digamesystems/LIDAR/docs/Heimdall Docs/FCC Label/FCC_Label.pdf

M

# Dígame Systems odel: DS-VC-LIDAR-LOR-1

FCC IDS: QLYRYLR896, 2AC7Z-ESPWROOM32

www.digamesystems.com Made in USA

### HEMDALL VCS Vehicle Counting System

M

# Dígame Systems odel: DS-VC-LIDAR-LOR-1

FCC IDS: QLYRYLR896, 2AC7Z-ESPWROOM32

www.digamesystems.com Made in USA

### HEMDALL VCS Vehicle Counting System

M

# Dígame Systems odel: DS-VC-LIDAR-LOR-1

FCC IDS: QLYRYLR896, 2AC7Z-ESPWROOM32

www.digamesystems.com Made in USA

### HEMDALL VCS Vehicle Counting System

M

# Dígame Systems odel: DS-VC-LIDAR-LOR-1

FCC IDS: QLYRYLR896, 2AC7Z-ESPWROOM32

www.digamesystems.com Made in USA

### HEMDALL VCS Vehicle Counting System

M

# Dígame Systems odel: DS-VC-LIDAR-LOR-1

FCC IDS: QLYRYLR896, 2AC7Z-ESPWROOM32

www.digamesystems.com Made in USA

### HEMDALL VCS Vehicle Counting System

M

# Dígame Systems odel: DS-VC-LIDAR-LOR-1

FCC IDS: QLYRYLR896, 2AC7Z-ESPWROOM32

www.digamesystems.com Made in USA

### HEMDALL VCS Vehicle Counting System

M

# Dígame Systems odel: DS-VC-LIDAR-LOR-1

FCC IDS: QLYRYLR896, 2AC7Z-ESPWROOM32

www.digamesystems.com Made in USA

### HEMDALL VCS Vehicle Counting System

M

# Dígame Systems odel: DS-VC-LIDAR-LOR-1

FCC IDS: QLYRYLR896, 2AC7Z-ESPWROOM32

www.digamesystems.com Made in USA

### HEMDALL VCS Vehicle Counting System

M

# Dígame Systems odel: DS-VC-LIDAR-LOR-1

FCC IDS: QLYRYLR896, 2AC7Z-ESPWROOM32

www.digamesystems.com Made in USA

### HEMDALL VCS Vehicle Counting System

M

# Dígame Systems odel: DS-VC-LIDAR-LOR-1

FCC IDS: QLYRYLR896, 2AC7Z-ESPWROOM32

www.digamesystems.com Made in USA

### HEMDALL VCS Vehicle Counting System

M

# Dígame Systems odel: DS-VC-LIDAR-LOR-1

FCC IDS: QLYRYLR896, 2AC7Z-ESPWROOM32

www.digamesystems.com Made in USA

### HEMDALL VCS Vehicle Counting System

M

# Dígame Systems odel: DS-VC-LIDAR-LOR-1

FCC IDS: QLYRYLR896, 2AC7Z-ESPWROOM32

www.digamesystems.com Made in USA

### HEMDALL VCS Vehicle Counting System

M

# Dígame Systems odel: DS-VC-LIDAR-LOR-1

FCC IDS: QLYRYLR896, 2AC7Z-ESPWROOM32

www.digamesystems.com Made in USA

### HEMDALL VCS Vehicle Counting System

M

# Dígame Systems odel: DS-VC-LIDAR-LOR-1

FCC IDS: QLYRYLR896, 2AC7Z-ESPWROOM32

www.digamesystems.com Made in USA

### HEMDALL VCS Vehicle Counting System

M

# Dígame Systems odel: DS-VC-LIDAR-LOR-1

FCC IDS: QLYRYLR896, 2AC7Z-ESPWROOM32

www.digamesystems.com Made in USA

### HEMDALL VCS Vehicle Counting System
