digamesystems/LIDAR/docs/Heimdall Docs/Product Brief/Heimdall VCS Digame Systems v 1.1.pdf

# Heimdall VCS

# ANONYMOUS, ACCURATE VEHICLE COUNTING— WITHOUT TOUCHING THE ROADWAY

# The Heimdall VCS is a cutting-edge vehicle counting system incorporating recent technology advancements in high-performance sensors, wireless connectivity, and artificial intelligence

to provide unprecedented performance at an affordable price.

# FEATURES AND FUNCTIONS

### - LIDAR-Based solution means vehicles can be counted without hardware on the roadway –

Allowing lower installation and maintenance costs.

### - Respects privacy – The system does not make use

of cameras.

- Outdoor Rated – IP67, NEMA4.

### - WiFi with optional LoRaWAN (Low power, Long Range RF link) or cellular connectivity. – Requires

no external wiring to the unit.

- Easy integration with back-end systems – Secure, HTTPs API.
- Battery-backed solar power for reliable, autonomous operation.

### - Accurate target determination at up to 12 meters

of range.

### - Advanced signal processing allows reliable

operation in rain and fog.

## HEIMDALL VCS SPECIFICATIONS

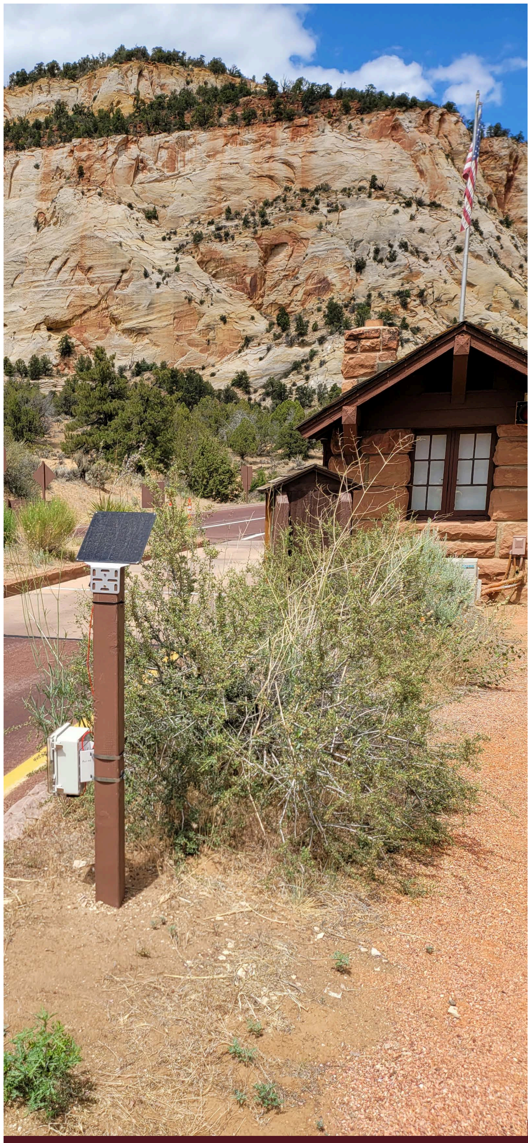
[picture p3: figure]

Use Case

LIDAR Sensor Specifications

Mounting / Power

Interface / Communications

Environmental

Vehicle counting
applications:

Vehicle speed:

Operating Range

Accuracy:

Field of View:

Frame Rate:

Counting Accuracy:

Mounting:

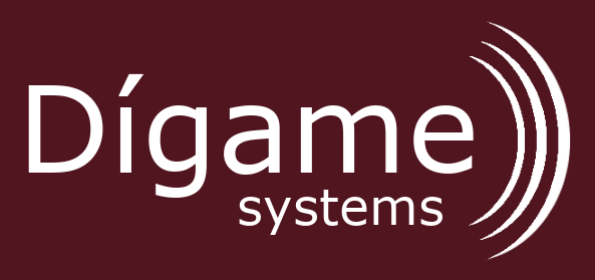
[picture p4: figure]

Input Voltage:

Power Consumption:

Battery:

Battery Type:

Protection:

Cellular service:

Security:

API:

Enclosure:

Operational Temperature:

Storage Temperature

Warranty:

WiFi, Cellular, LoRaWan:

1-2 Lanes of traffic.

Up to 60 MPH

0.1 – 12 meters

+/- 5 cm

3.6 degrees

100 Hz

>95% counting accuracy at distances < 12

### meters and speeds < 60 MPH. (Performance may vary in extreme weather conditions.)

Surface mount or pole mount (custom options available)

5-7 VDC (DC power supply or supplied solar panel output)

1 Watt typ.

Capacity: 12,800mAh, 47 Watt Hours

Li-Ion

Short circuit over charge, over discharge, over temperature (45°Input Cutoff, 60° Output Cutoff), under temperature (0° Input Cutoff, -20° Output Cutoff)

WiFi included. Cellular and LoRaWAN optional.

HTTPs, WPA under WiFI

JSON-based for easy integration

High Impact UV resistant polycarbonate, IP67/NEMA4

20° to + 60°

-20°C to +60°C

Replacement, 3 years parts and labor.

Dígame Systems

88 E San Fernando St. Suite 1511 San Jose, CA 95113

+1 408.840.9871
info@digamesystems.com

## Ready to get started?

Contact info@digamesystems.com

Not included.
