digamesystems/LIDAR/docs/shuttleCutFiles/TF-mini Plus Diagrams/982B110B7F3D70D8.png

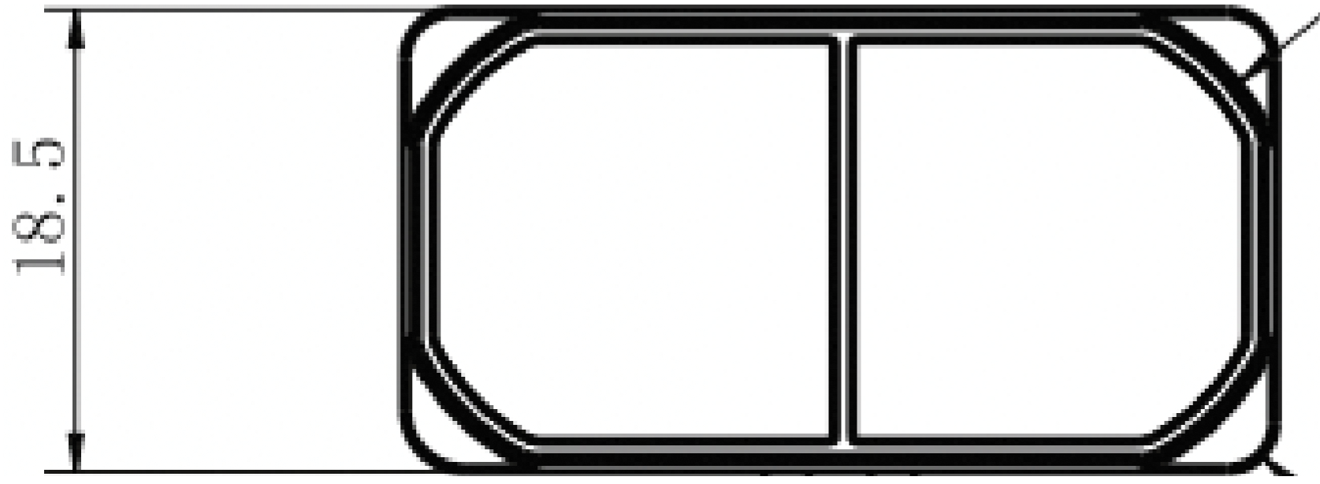
docs/shuttleCutFiles/TF-mini Plus Diagrams/982B110B7F3D70D8.png
