digamesystems/LIDAR/docs/shuttleCutFiles/TF-mini Plus Diagrams/982B110B7F3D70DF.jpg

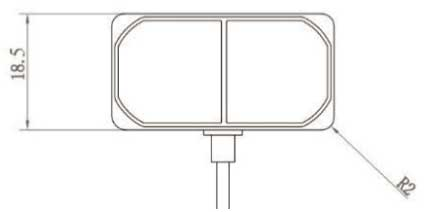
docs/shuttleCutFiles/TF-mini Plus Diagrams/982B110B7F3D70DF.jpg
