digamesystems/LIDAR/images/200x200_BMPS/digame.bmp

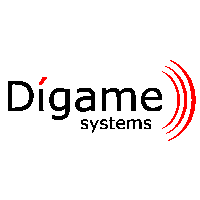
images/200x200_BMPS/digame.bmp
