digamesystems/LIDAR/images/200x200_BMPS/parkdata.bmp

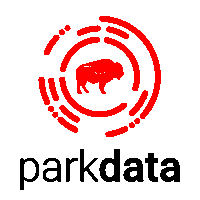
images/200x200_BMPS/parkdata.bmp
