digamesystems/LIDAR/images/200x200_BMPS/title.bmp

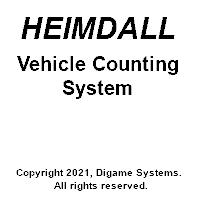
images/200x200_BMPS/title.bmp
