digamesystems/LIDAR/images/20210713_194357.jpg

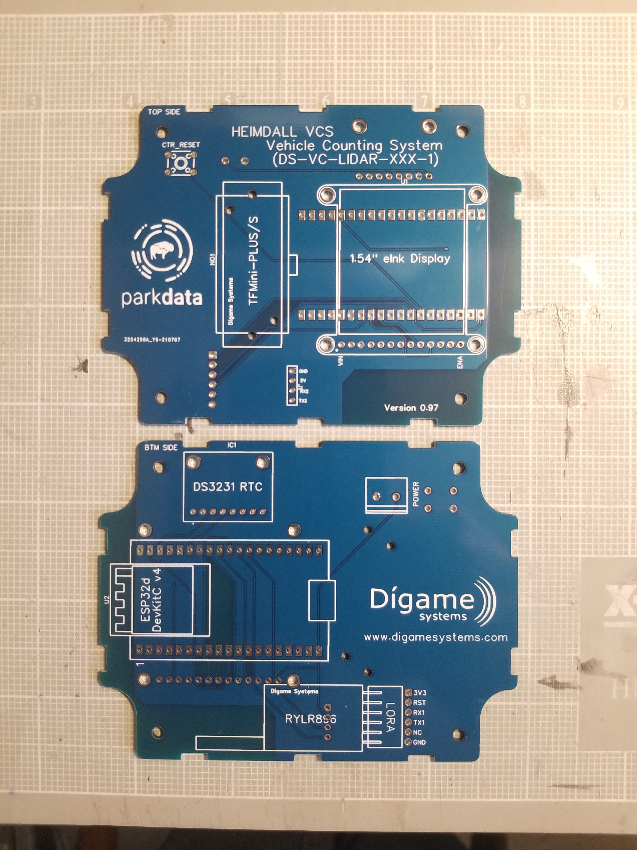
images/20210713_194357.jpg
