digamesystems/LIDAR/images/20210716_140122.jpg

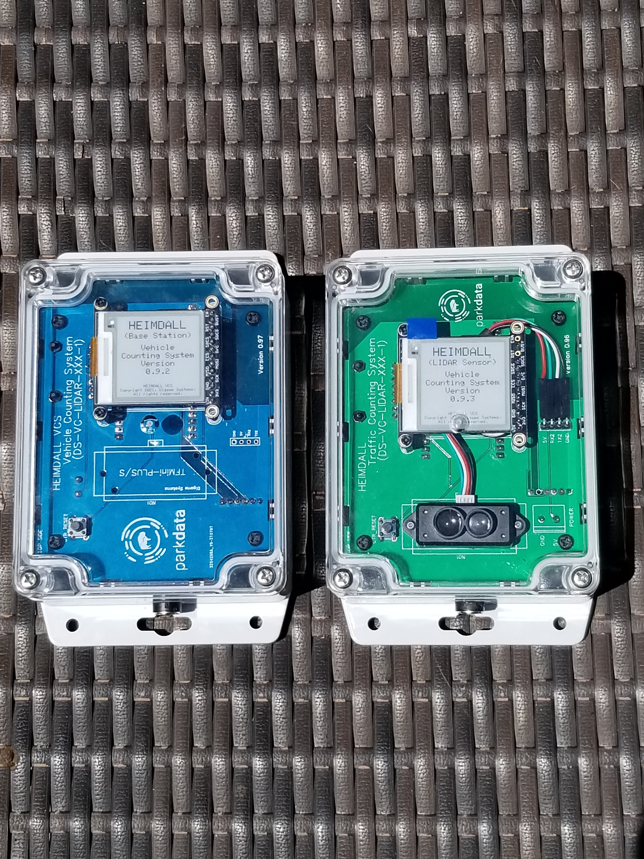
images/20210716_140122.jpg
