digamesystems/LIDAR/images/20210716_140350.jpg

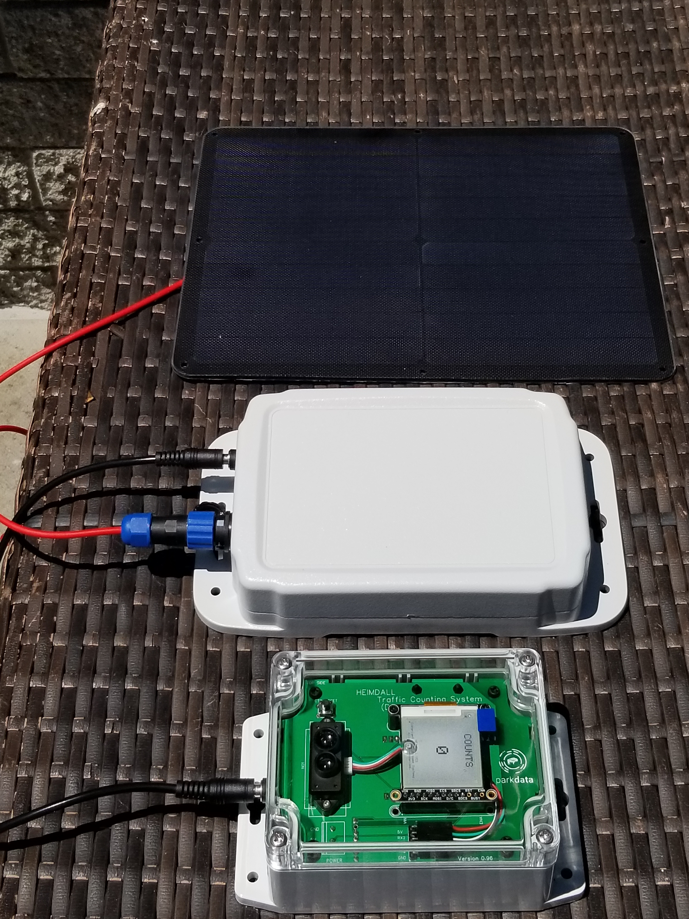
images/20210716_140350.jpg
