digamesystems/LIDAR/images/20210716_140622.jpg

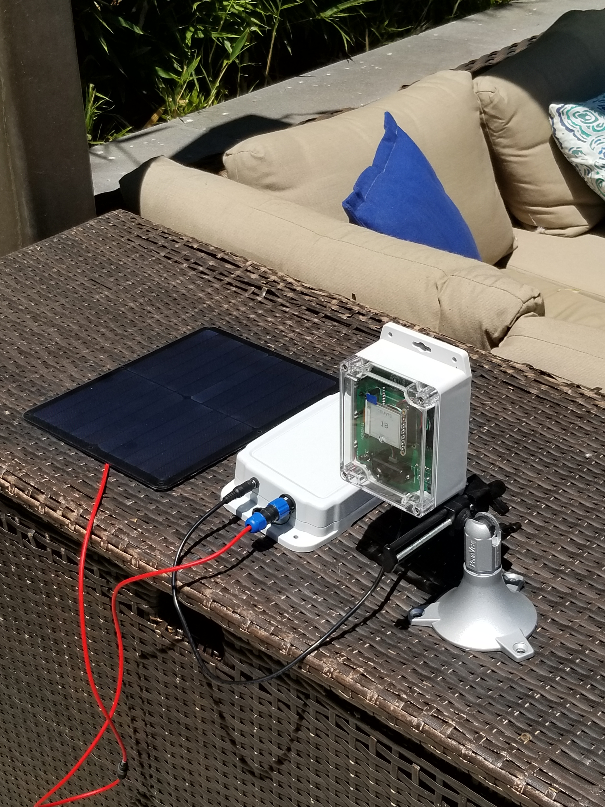
images/20210716_140622.jpg
