digamesystems/LIDAR/images/20210716_140631.jpg

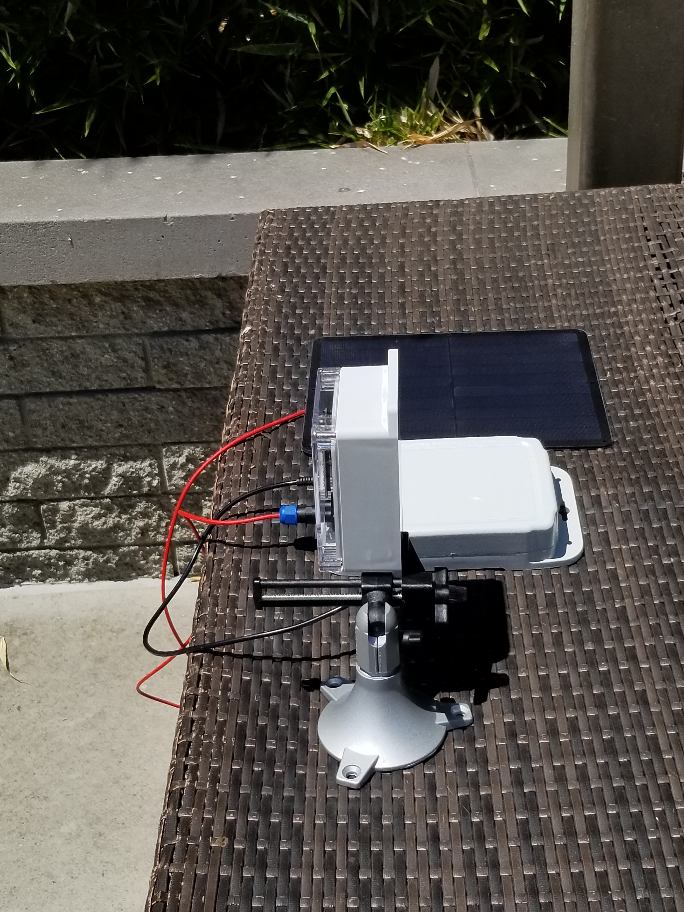
images/20210716_140631.jpg
