digamesystems/LIDAR/images/20210716_140637.jpg

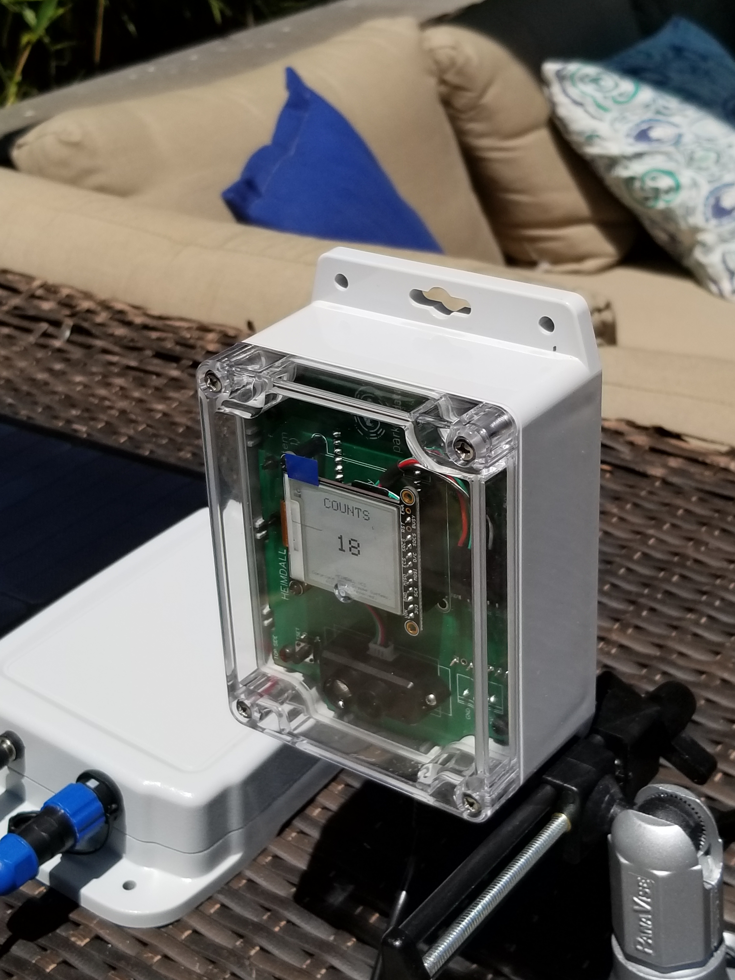
images/20210716_140637.jpg
