digamesystems/LIDAR/images/Heimdall Pics/2022-01-09 10.08.08.jpg

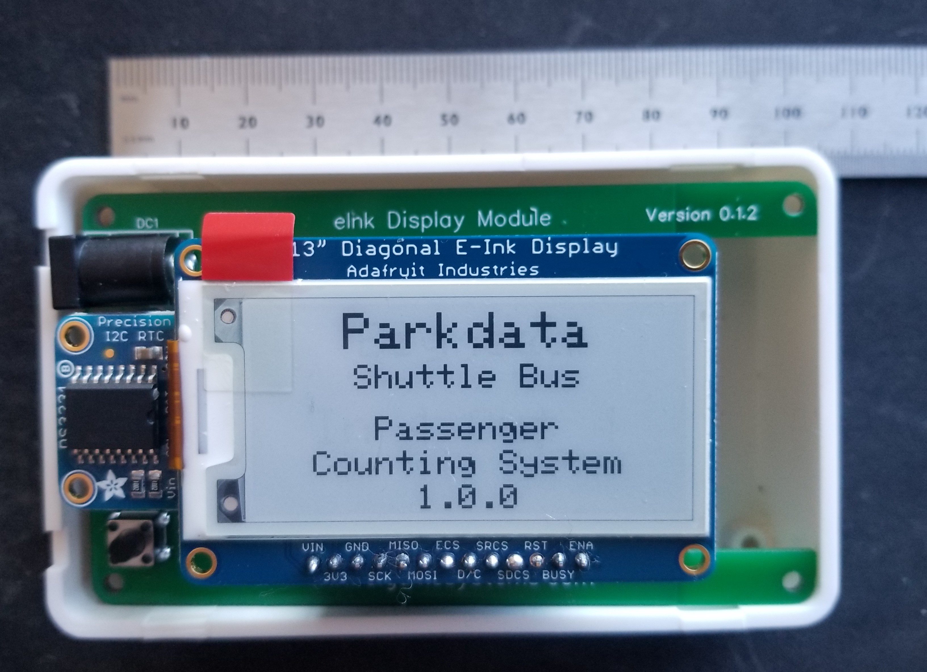
images/Heimdall Pics/2022-01-09 10.08.08.jpg
