digamesystems/LIDAR/images/Heimdall Pics/2022-01-11 13.43.02.jpg

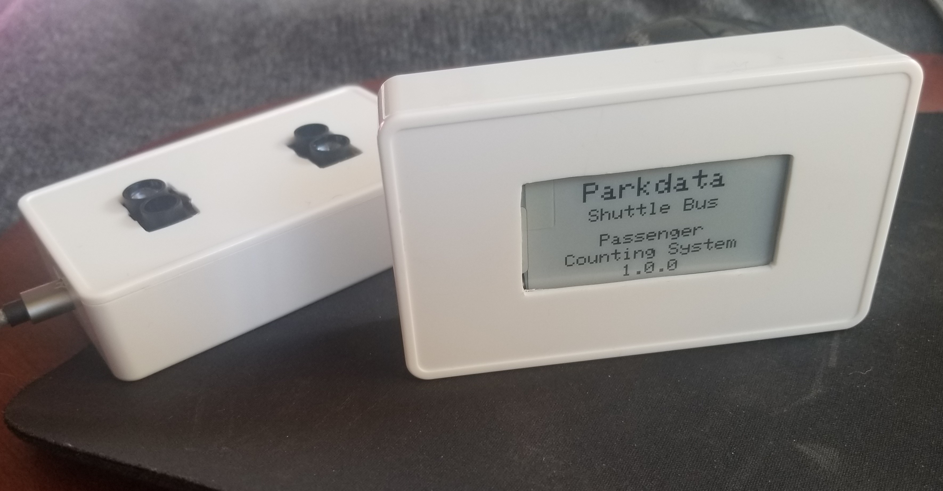
images/Heimdall Pics/2022-01-11 13.43.02.jpg
