digamesystems/LIDAR/images/Heimdall Pics/EastRadar_Dec21.PNG

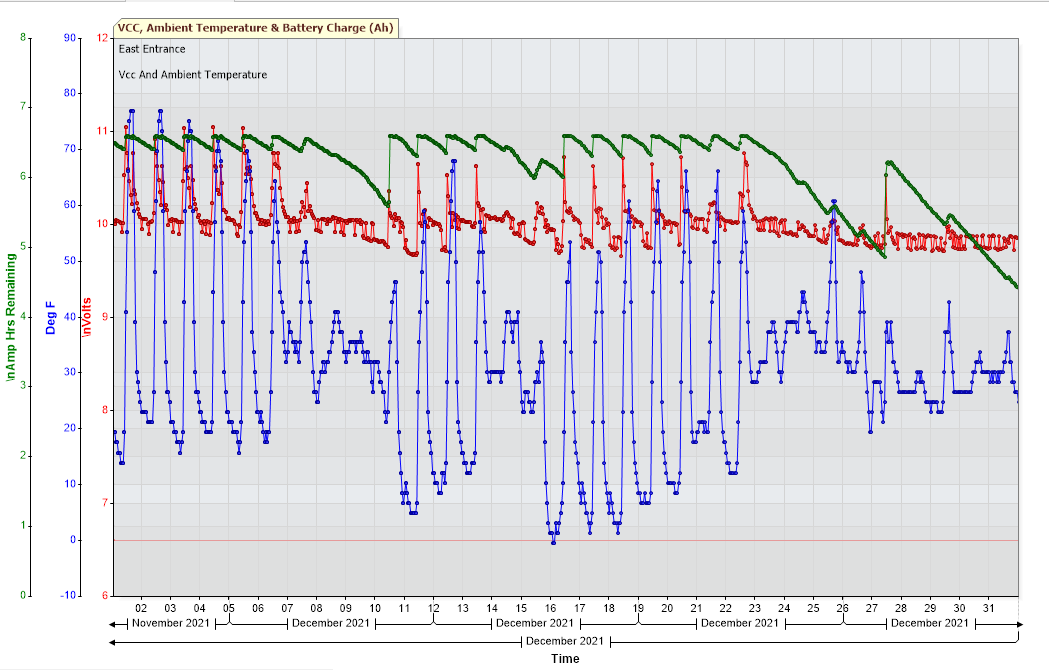
images/Heimdall Pics/EastRadar_Dec21.PNG
