digamesystems/LIDAR/images/Heimdall Pics/Zion Visitors Center 2.jpg

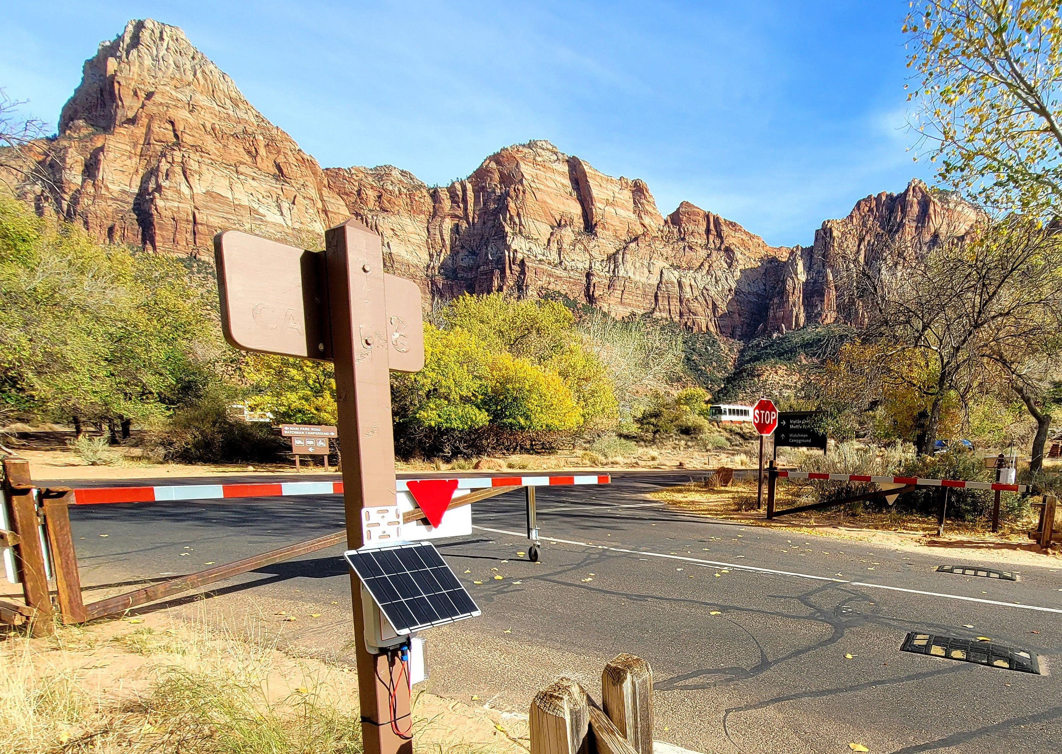
images/Heimdall Pics/Zion Visitors Center 2.jpg
