digamesystems/LIDAR/images/LoRa Examples/LoRa Tx and Rx Examples Working Together.png

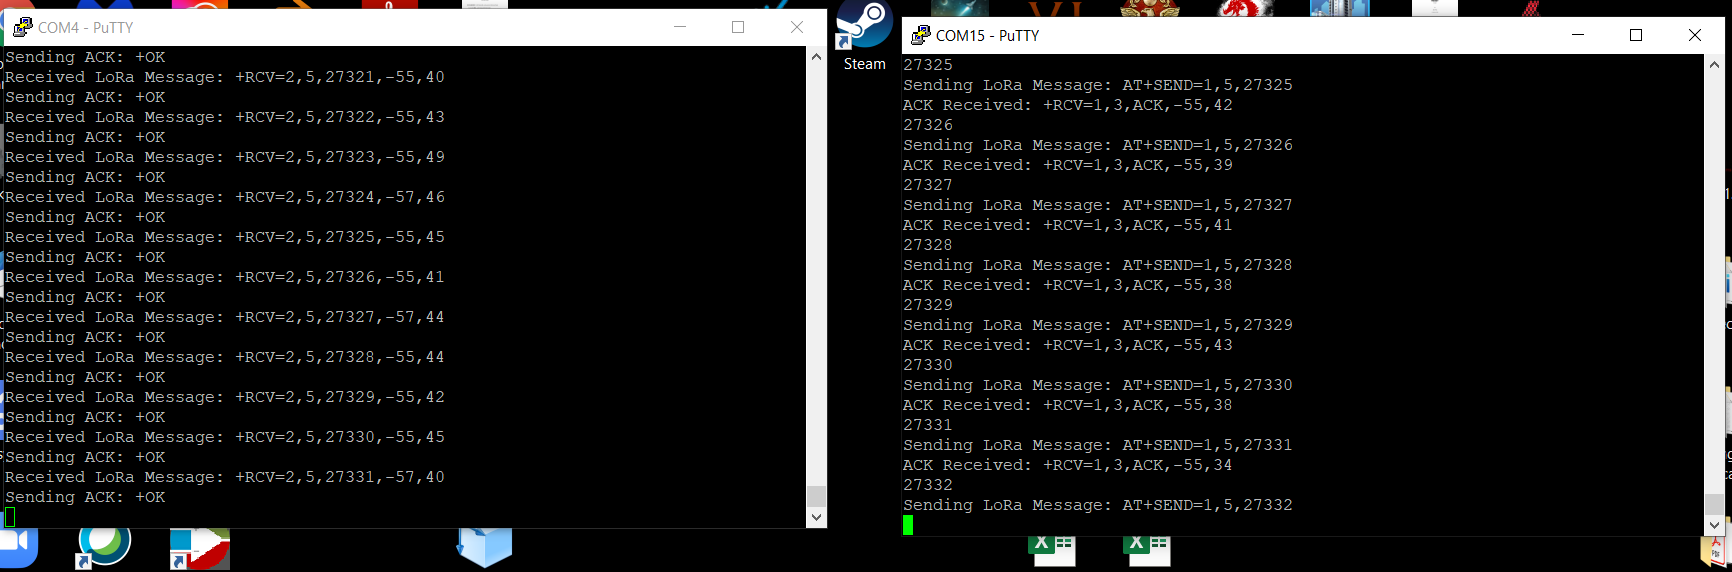
images/LoRa Examples/LoRa Tx and Rx Examples Working Together.png
