digamesystems/LIDAR/images/Shuttle Counter Pics/2021-12-30 08.01.03.jpg

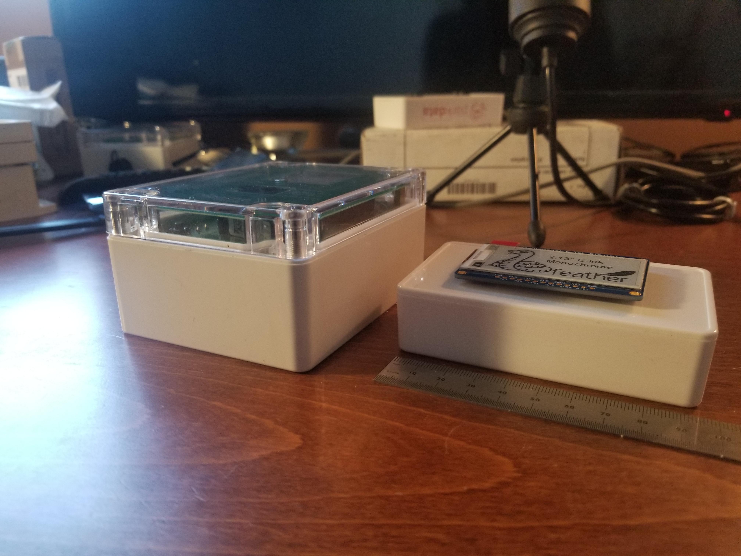
images/Shuttle Counter Pics/2021-12-30 08.01.03.jpg
