digamesystems/LIDAR/images/Shuttle Counter Pics/2022-01-10 12.27.30.jpg

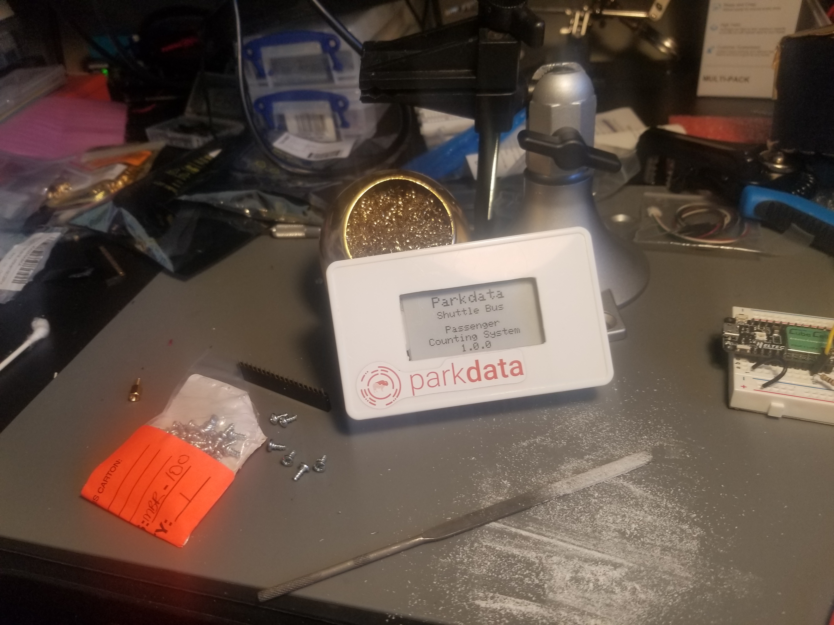
images/Shuttle Counter Pics/2022-01-10 12.27.30.jpg
