digamesystems/LIDAR/images/Shuttle Counter Pics/2022-01-20 13.23.47.jpg

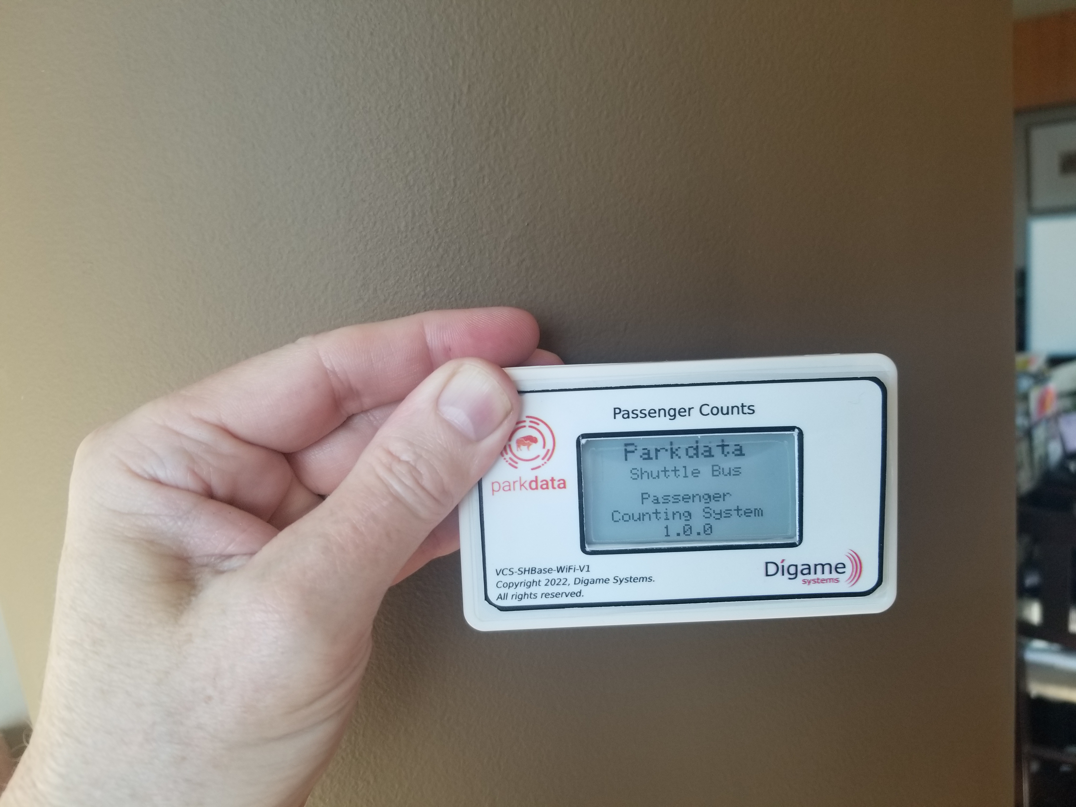
images/Shuttle Counter Pics/2022-01-20 13.23.47.jpg
