digamesystems/LIDAR/images/Shuttle Counter Pics/2022-03-01 12.52.25.jpg

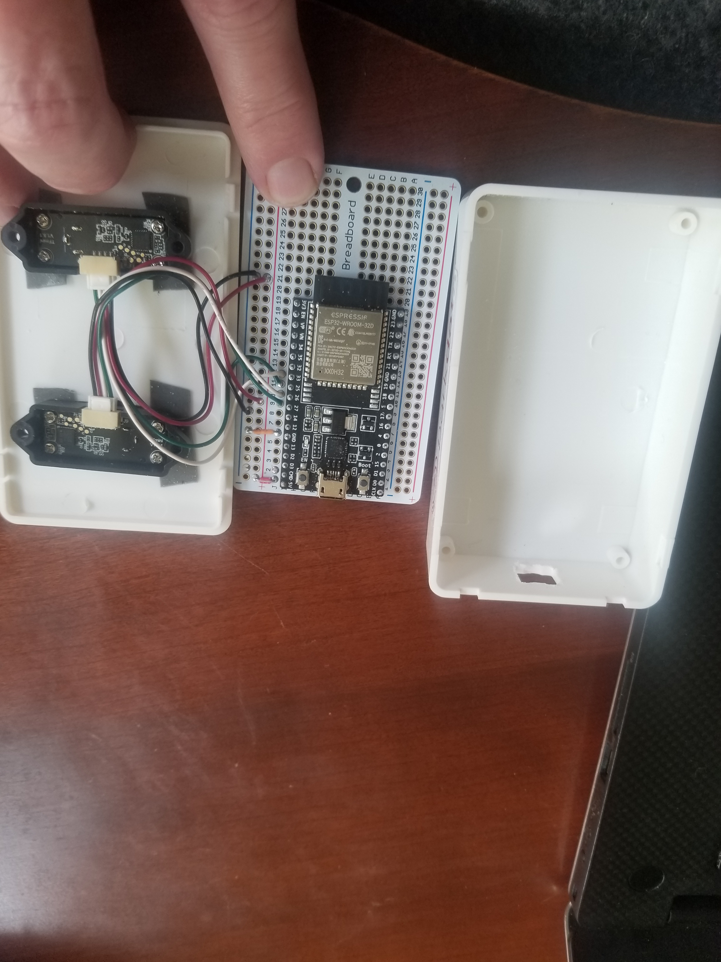
images/Shuttle Counter Pics/2022-03-01 12.52.25.jpg
