digamesystems/LIDAR/images/Shuttle Counter Pics/2022-03-01 12.52.33.jpg

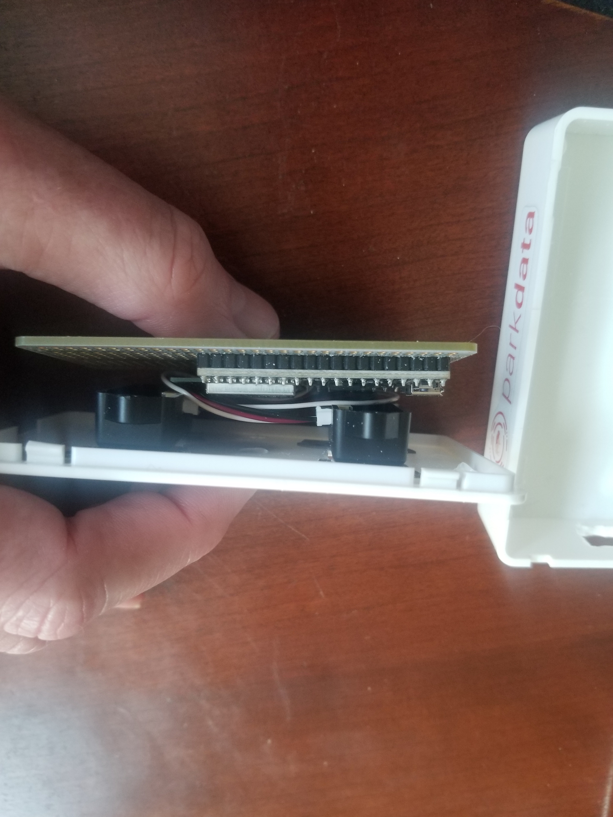
images/Shuttle Counter Pics/2022-03-01 12.52.33.jpg
