digamesystems/LIDAR/images/Shuttle Counter Pics/20220109_121842.jpg

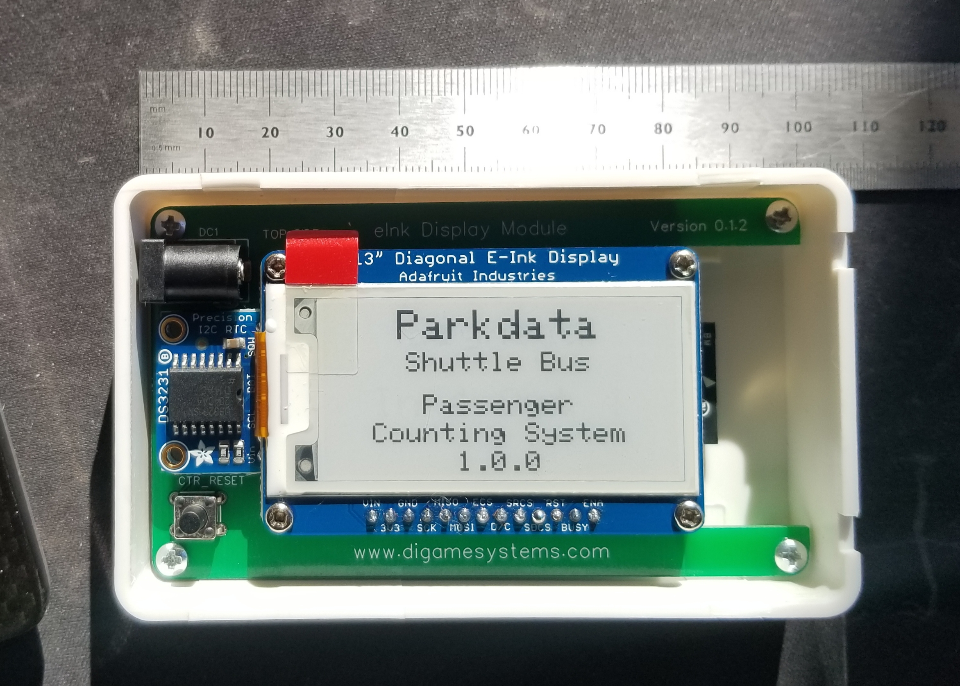
images/Shuttle Counter Pics/20220109_121842.jpg
