digamesystems/LIDAR/images/Shuttle Counter Pics/Image from iOS3.jpg

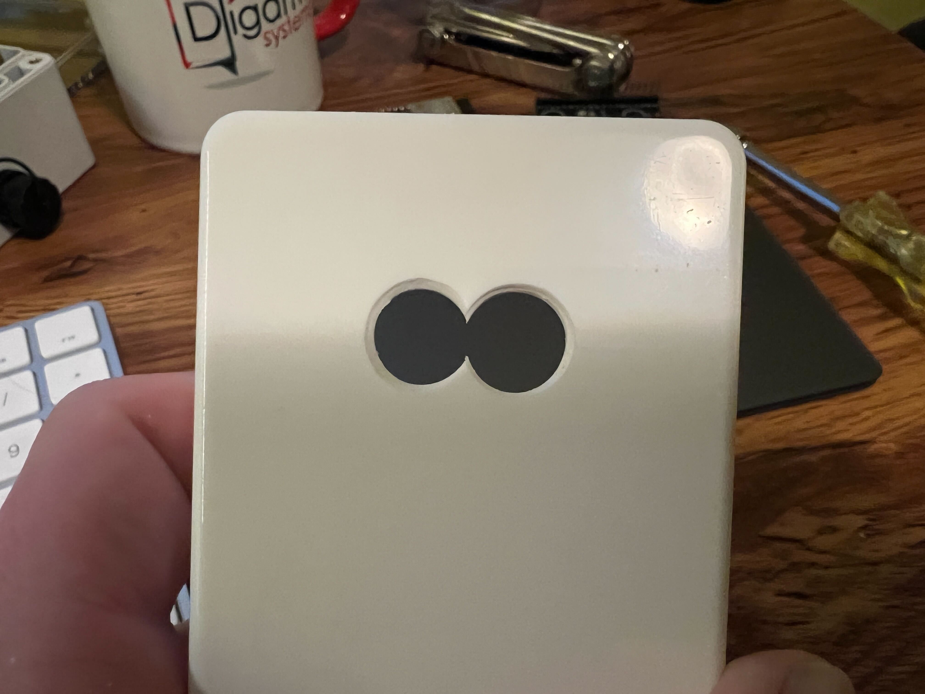
images/Shuttle Counter Pics/Image from iOS3.jpg
