digamesystems/LIDAR/images/Shuttle Counter Pics/Image from iOS 2.jpg

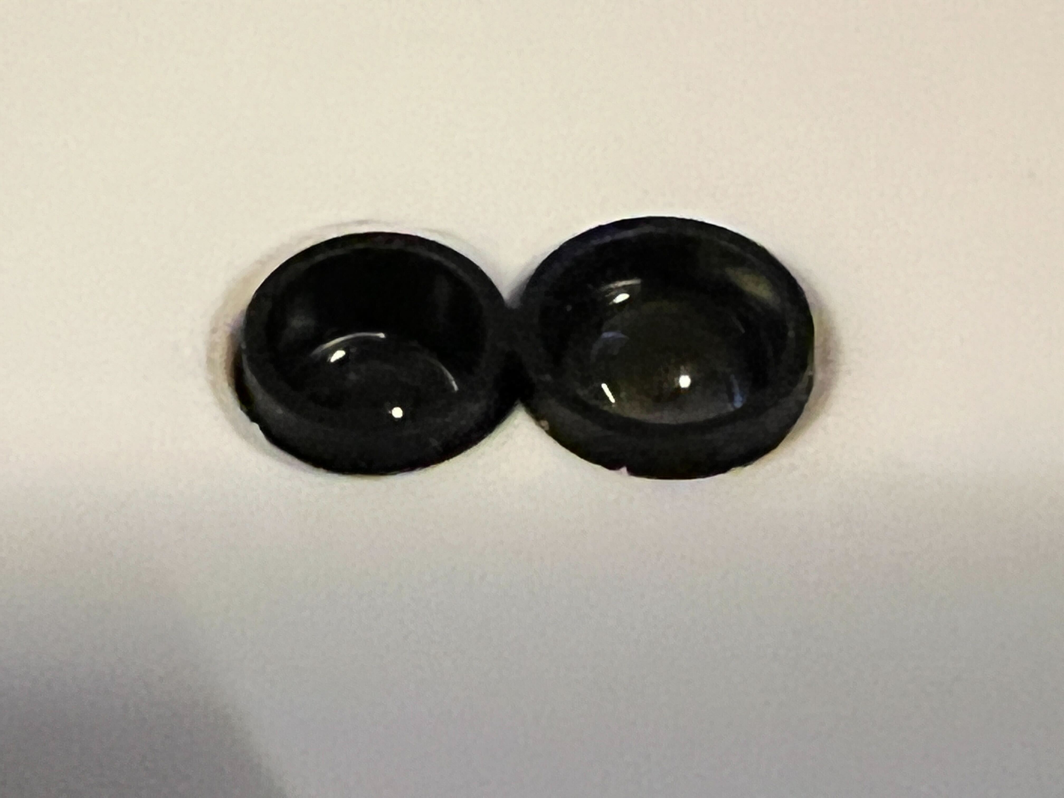
images/Shuttle Counter Pics/Image from iOS 2.jpg
