digamesystems/LIDAR/images/Shuttle Counter Pics/Image from iOS.jpg

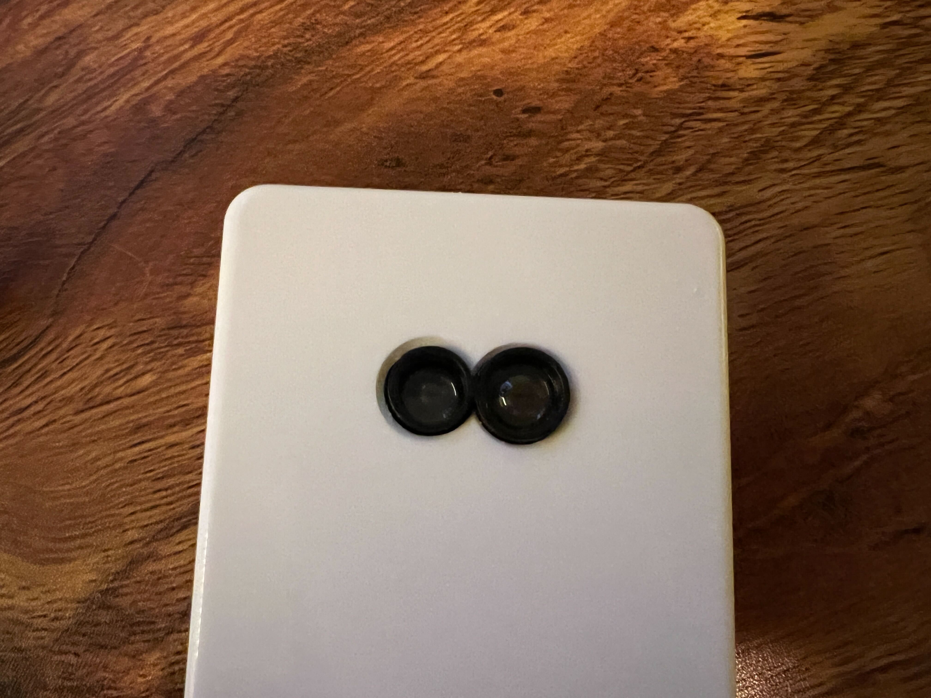
images/Shuttle Counter Pics/Image from iOS.jpg
