digamesystems/LIDAR/images/Shuttle Counter/20211229_122132.jpg

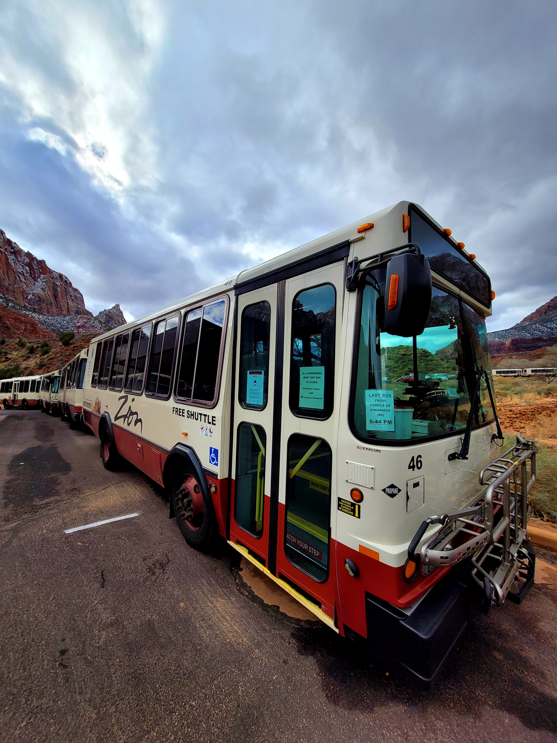
images/Shuttle Counter/20211229_122132.jpg
