digamesystems/LIDAR/images/Shuttle Counter/countingFingers.png

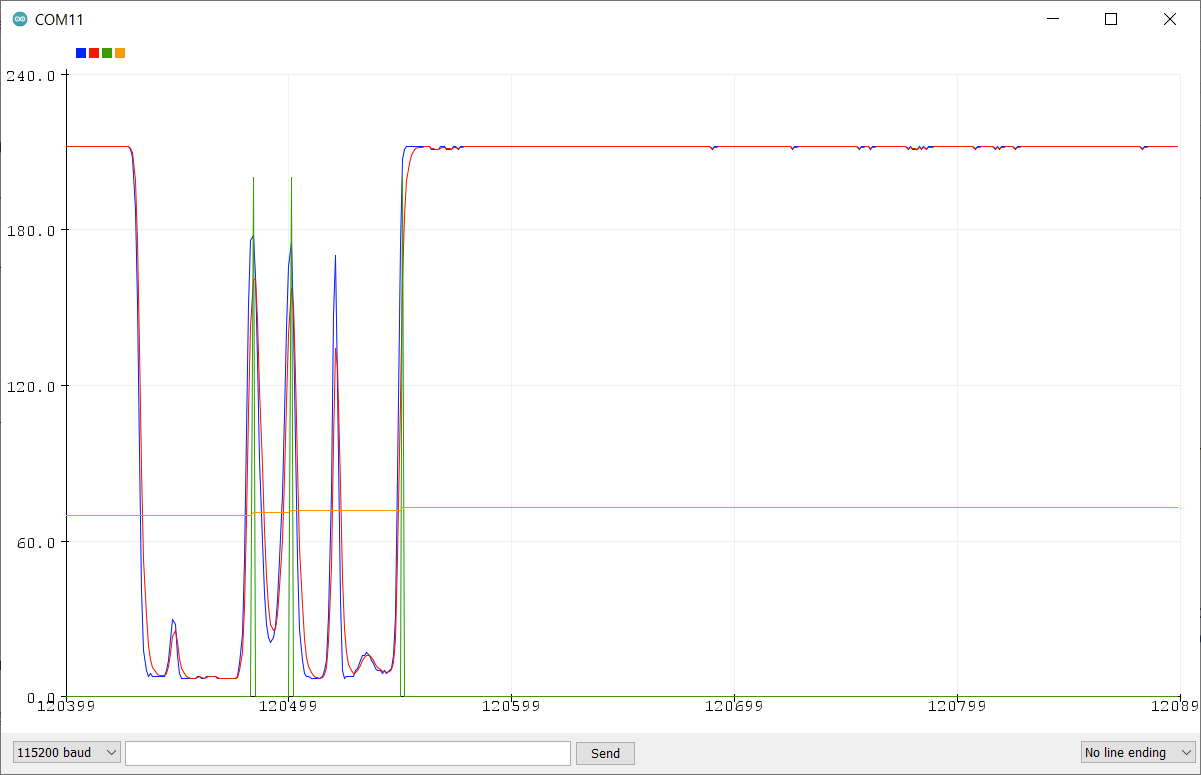
images/Shuttle Counter/countingFingers.png
