digamesystems/LIDAR/images/Shuttle Counter/filteredLIDARSignal.png

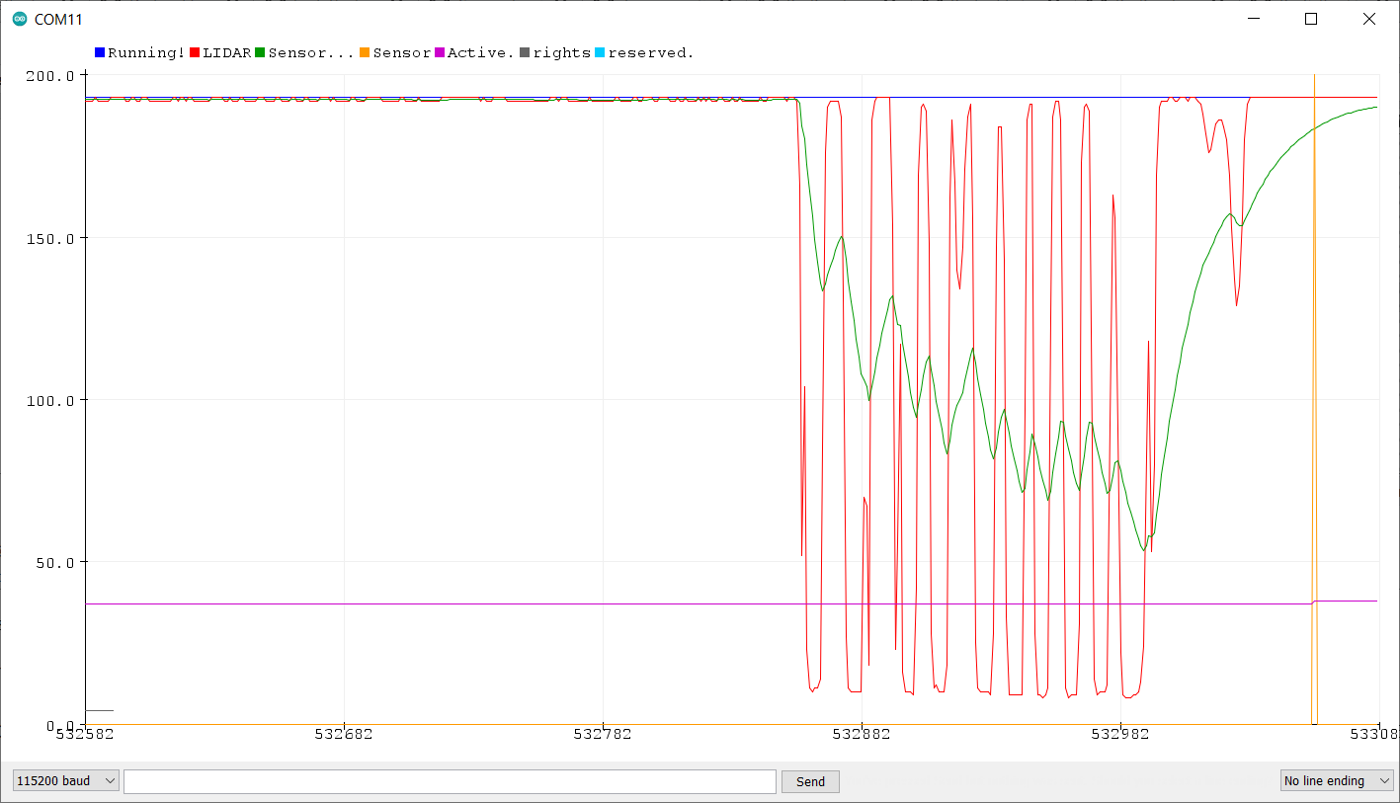
images/Shuttle Counter/filteredLIDARSignal.png
