digamesystems/LIDAR/images/Shuttle Counter/tfminiplusBeamWidth.png

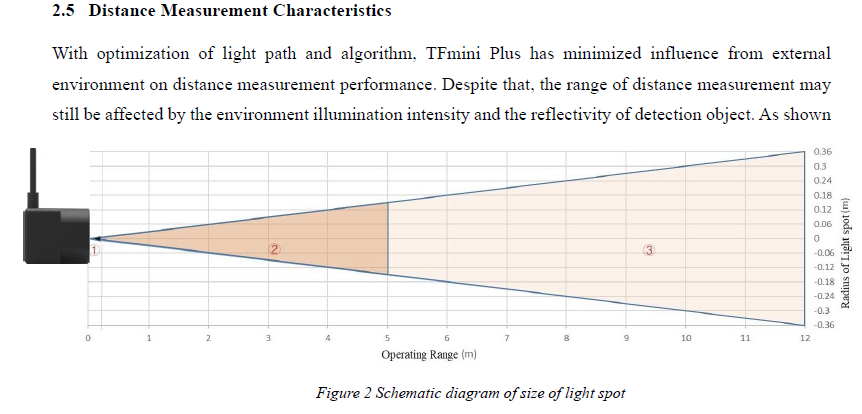
images/Shuttle Counter/tfminiplusBeamWidth.png
