digamesystems/LIDAR/images/Vehicle Counter/20201228_115122.jpg

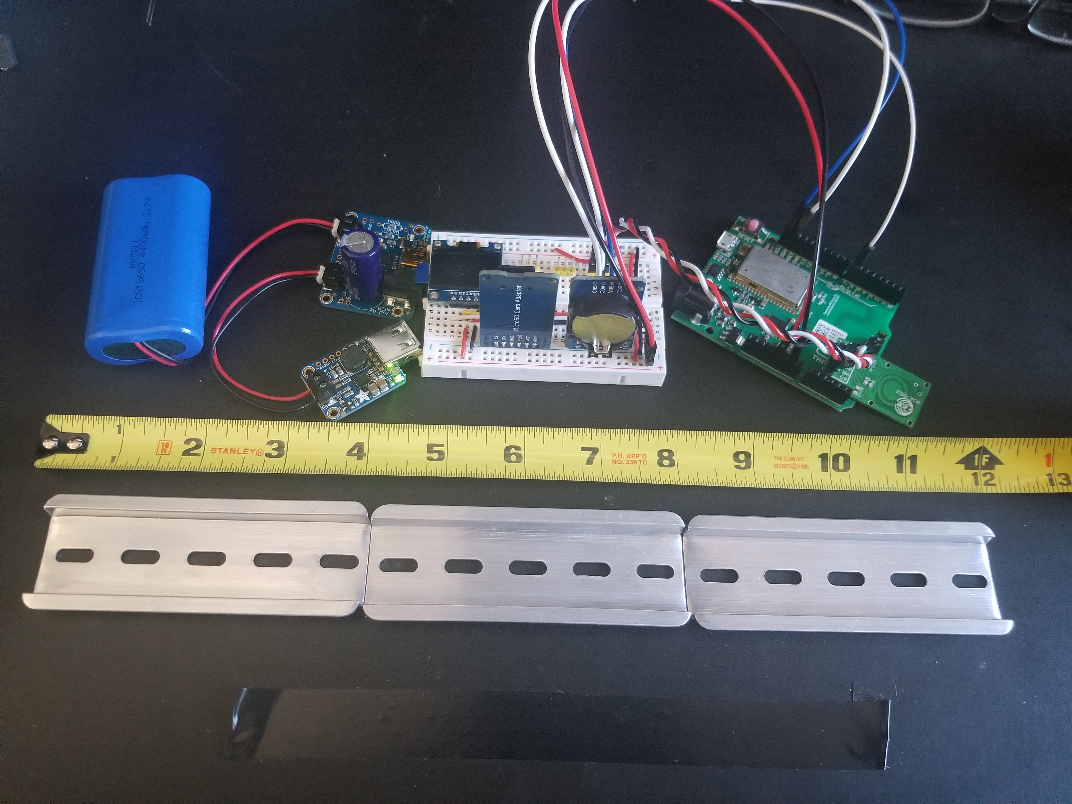
images/Vehicle Counter/20201228_115122.jpg
