digamesystems/LIDAR/images/Vehicle Counter/20201228_115124.jpg

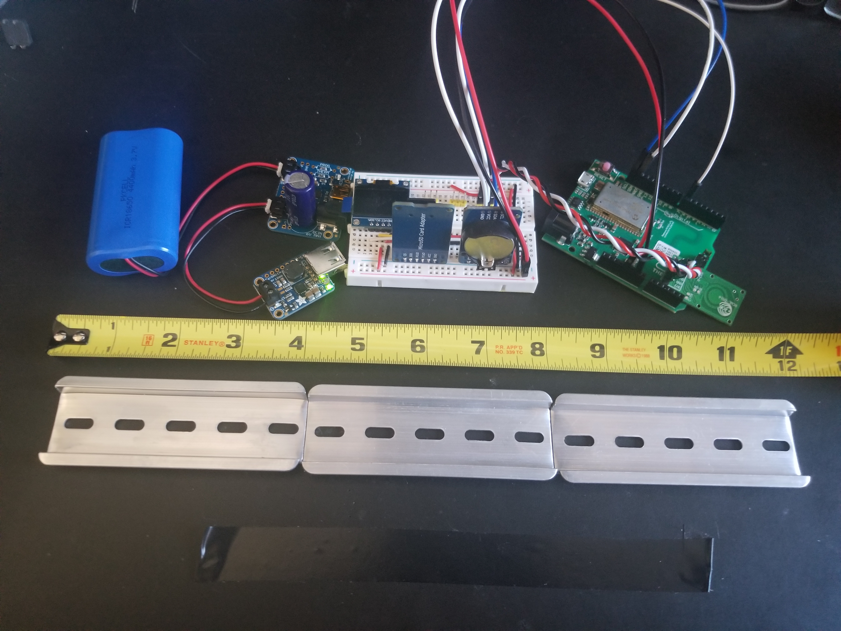
images/Vehicle Counter/20201228_115124.jpg
