digamesystems/LIDAR/images/Vehicle Counter/20210312_141206.jpg

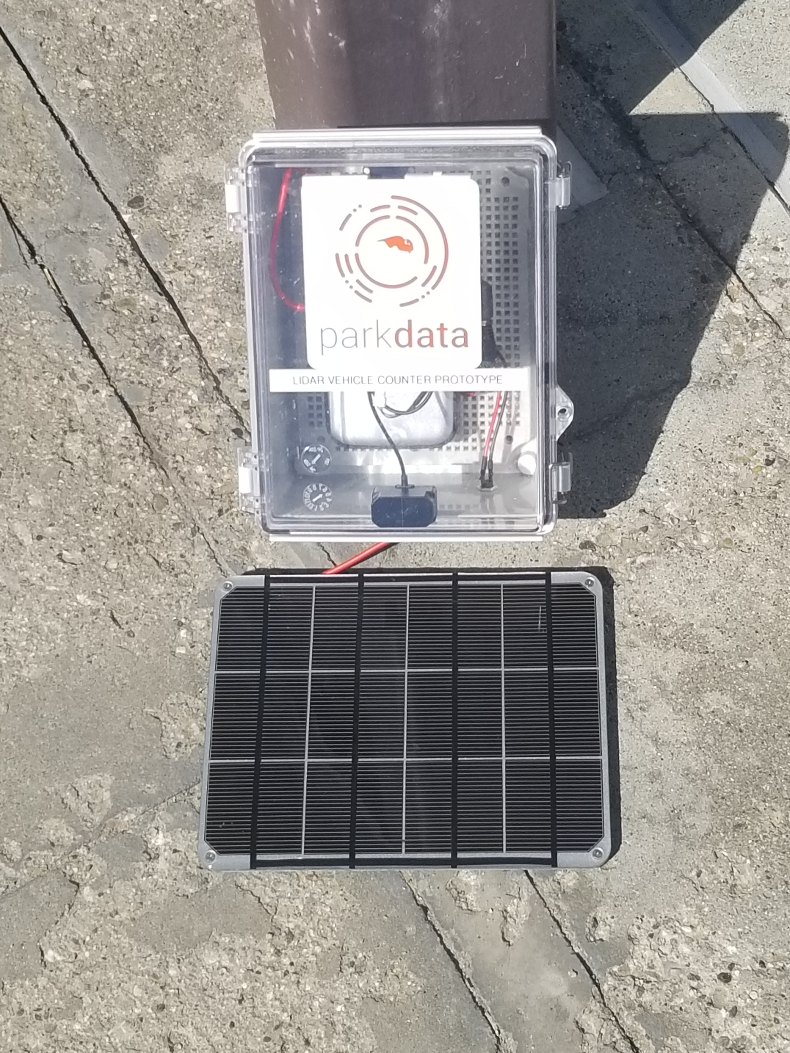
images/Vehicle Counter/20210312_141206.jpg
