digamesystems/LIDAR/images/Vehicle Counter/20210315_130030 zoom.jpg

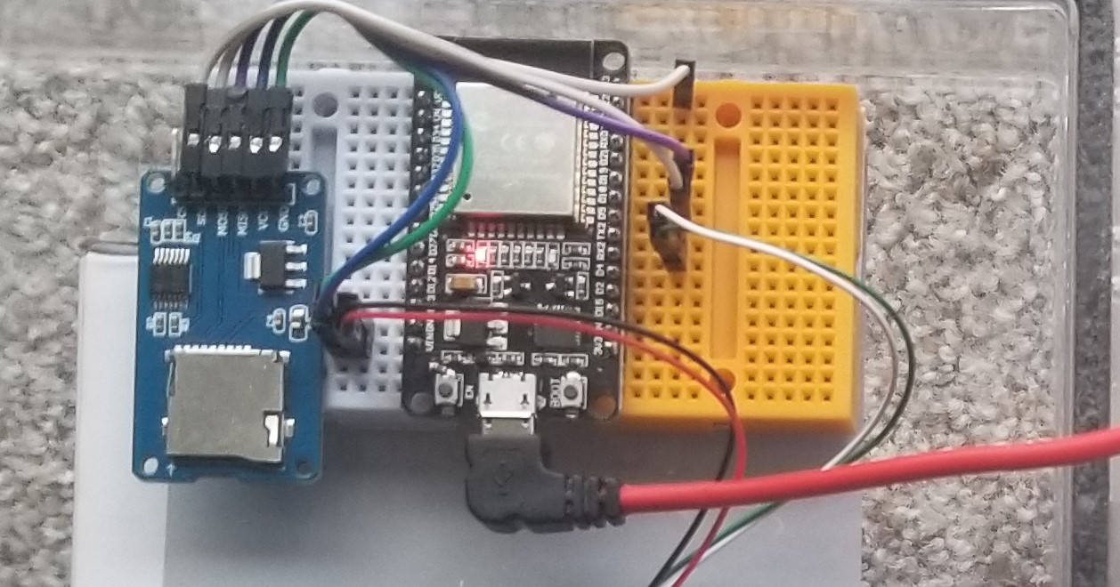
images/Vehicle Counter/20210315_130030 zoom.jpg
