digamesystems/LIDAR/images/Vehicle Counter/20210509_163343.jpg

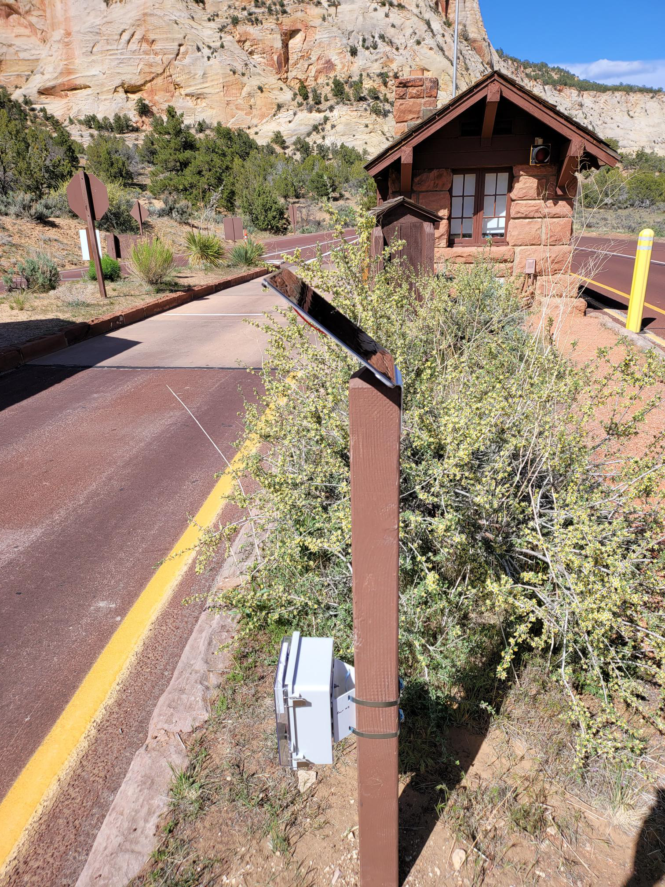
images/Vehicle Counter/20210509_163343.jpg
