digamesystems/LIDAR/images/Vehicle Counter/20210514_175608.jpg

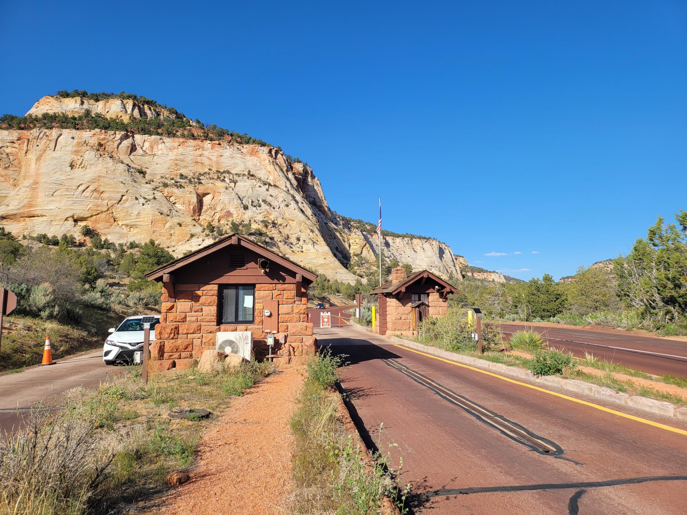
images/Vehicle Counter/20210514_175608.jpg
