digamesystems/LIDAR/images/Vehicle Counter/20210520_163920.jpg

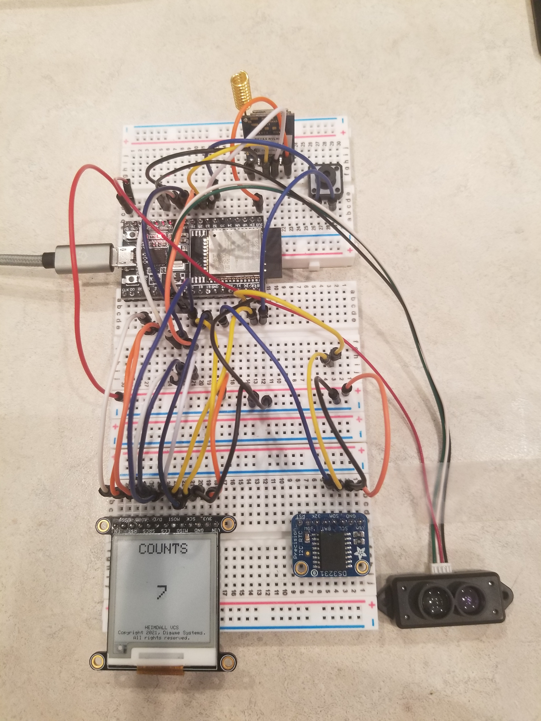
images/Vehicle Counter/20210520_163920.jpg
