digamesystems/LIDAR/images/Vehicle Counter/20211015_151012.jpg

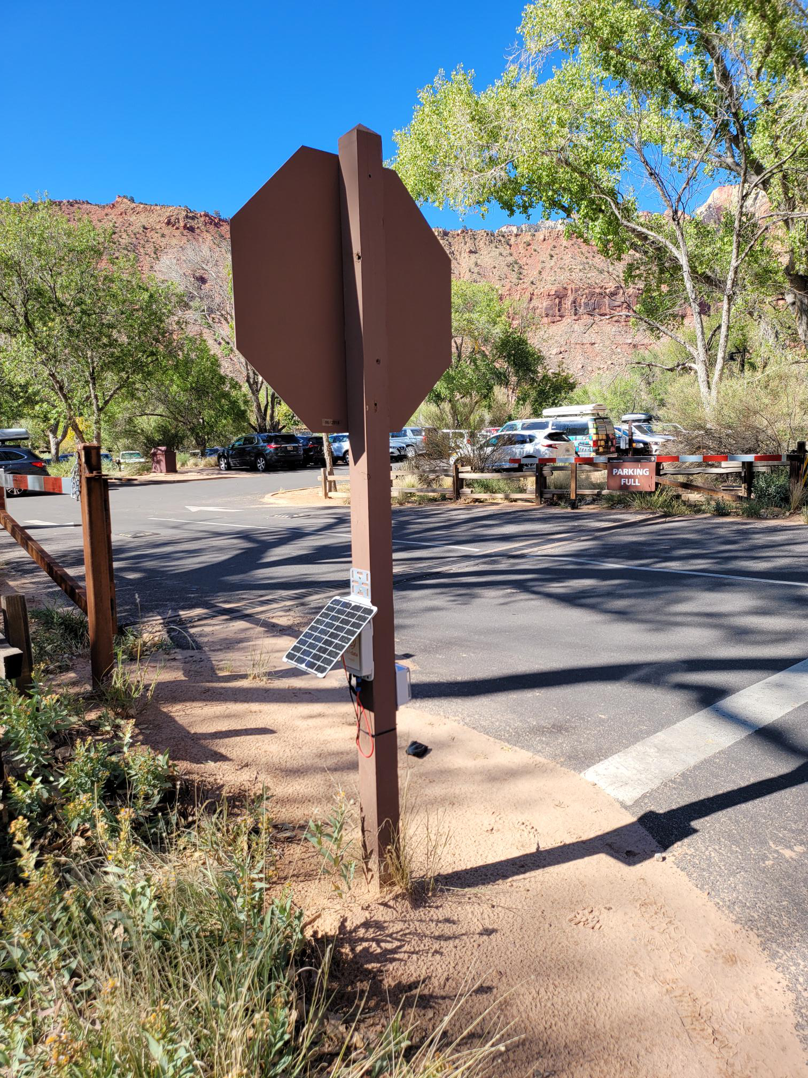
images/Vehicle Counter/20211015_151012.jpg
