digamesystems/LIDAR/images/Vehicle Counter/20211015_151321.jpg

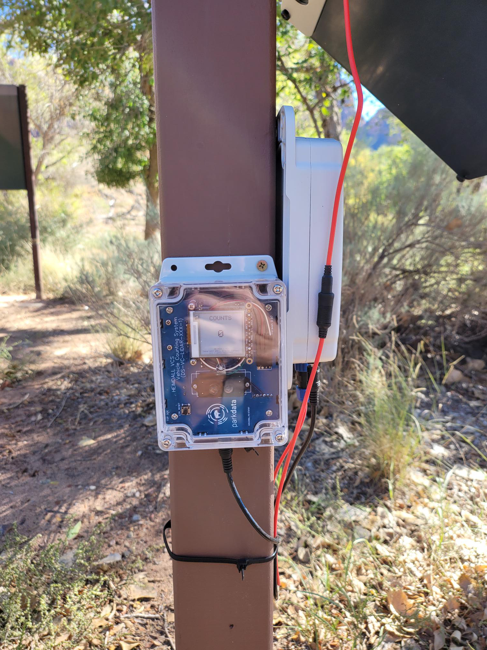
images/Vehicle Counter/20211015_151321.jpg
