digamesystems/LIDAR/images/Vehicle Counter/20211015_151425.jpg

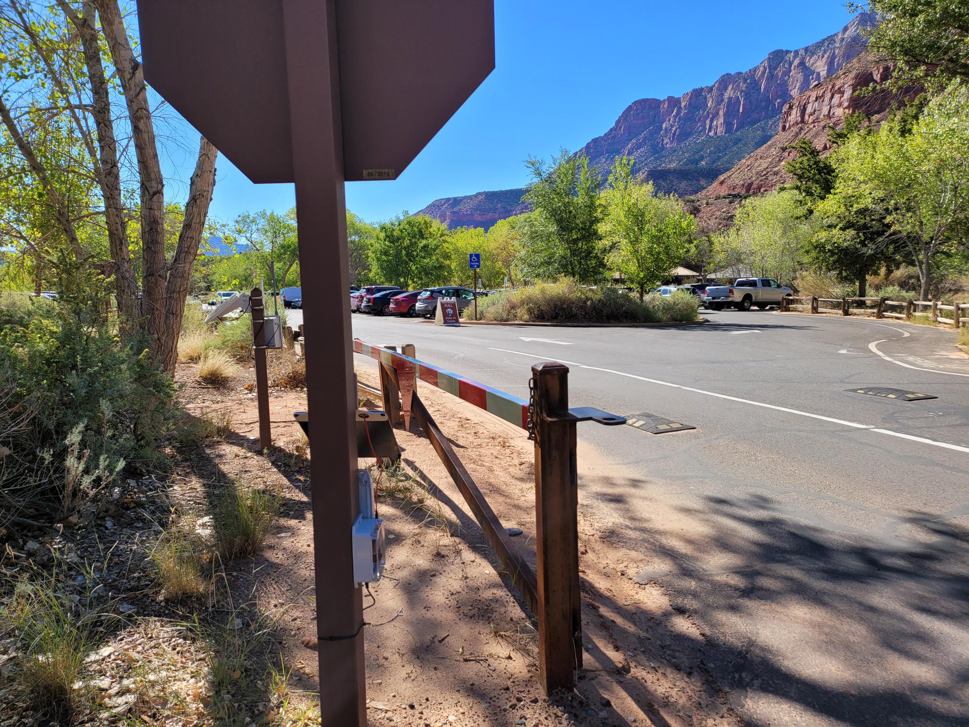
images/Vehicle Counter/20211015_151425.jpg
