digamesystems/LIDAR/images/Vehicle Counter/External View.jpg

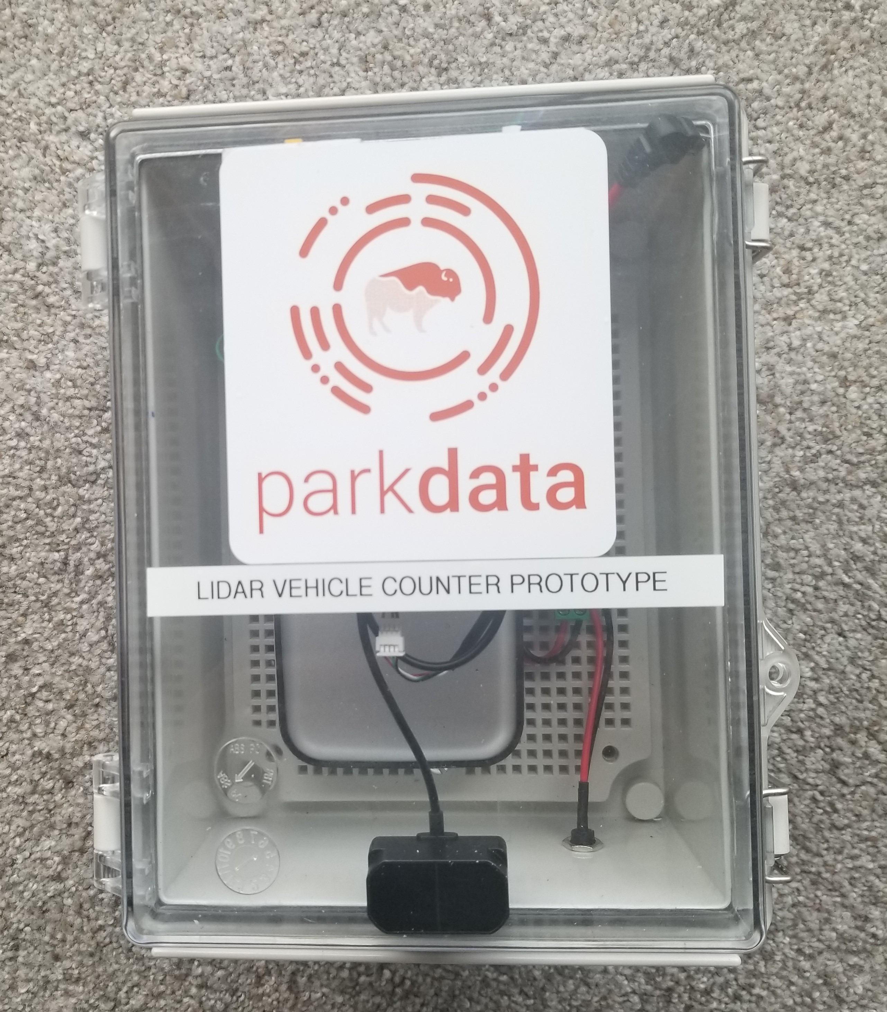
images/Vehicle Counter/External View.jpg
