digamesystems/LIDAR/images/Vehicle Counter/Inside view.jpg

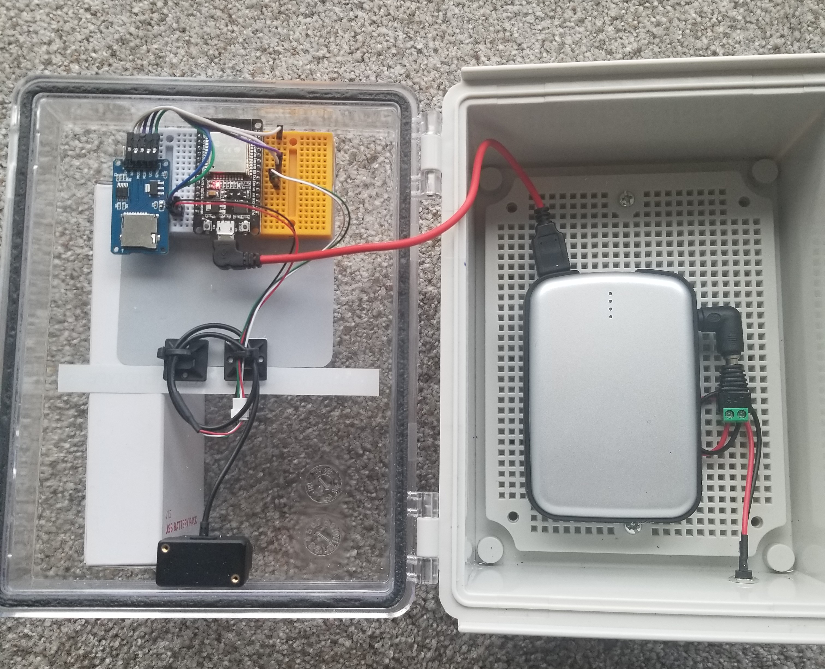
images/Vehicle Counter/Inside view.jpg
