digamesystems/LIDAR/images/Shuttle Counter/0.92 Board Testing Crop.jpg

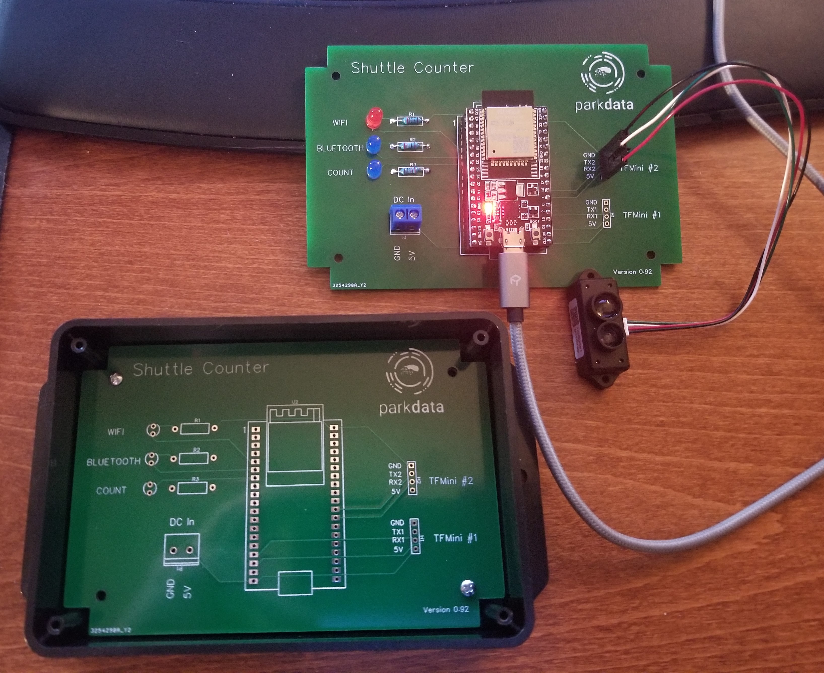
images/Shuttle Counter/0.92 Board Testing Crop.jpg
