digamesystems/LIDAR/images/Shuttle Counter/0.92 Board Testing.jpg

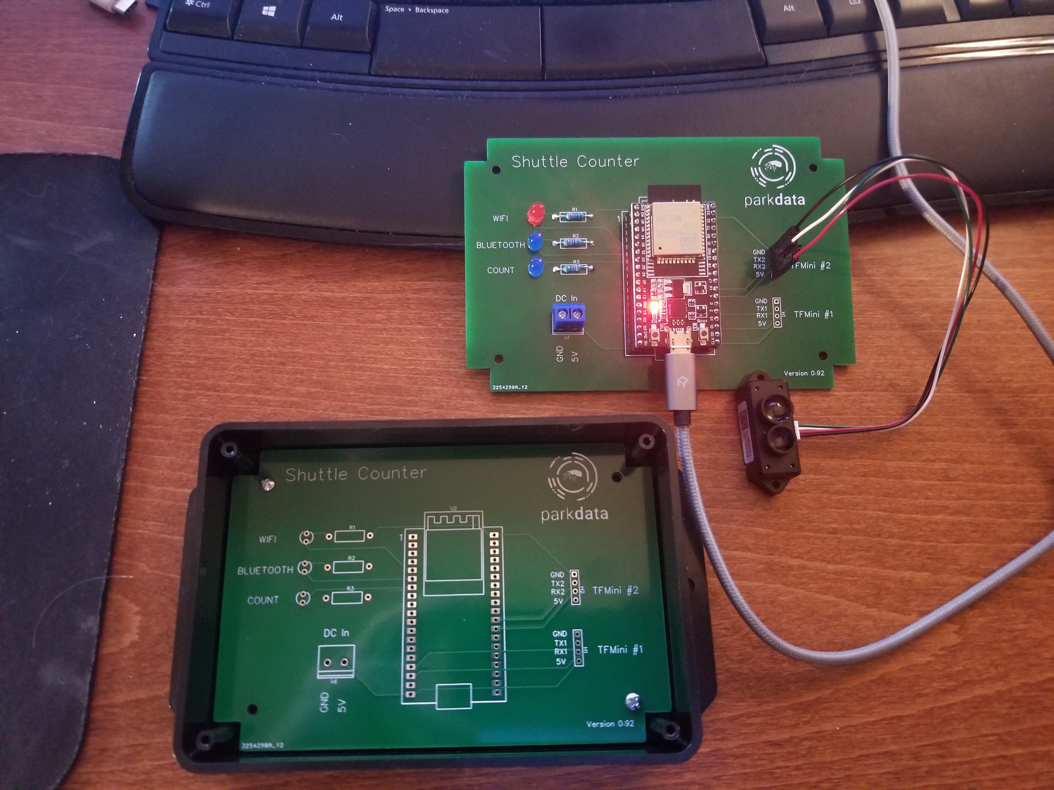
images/Shuttle Counter/0.92 Board Testing.jpg
