digamesystems/LIDAR/images/Shuttle Counter/smoothingExperiments.png

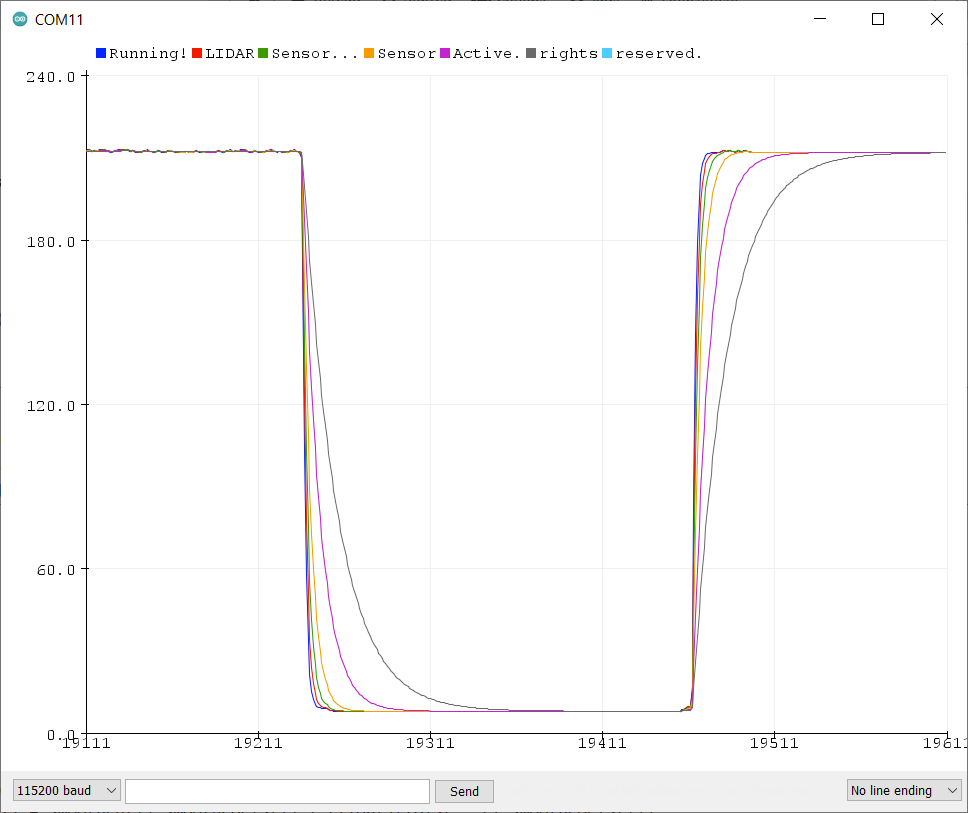
images/Shuttle Counter/smoothingExperiments.png
