digamesystems/LIDAR/docs/Polycase/LP-61/LP-61F PDF.pdf

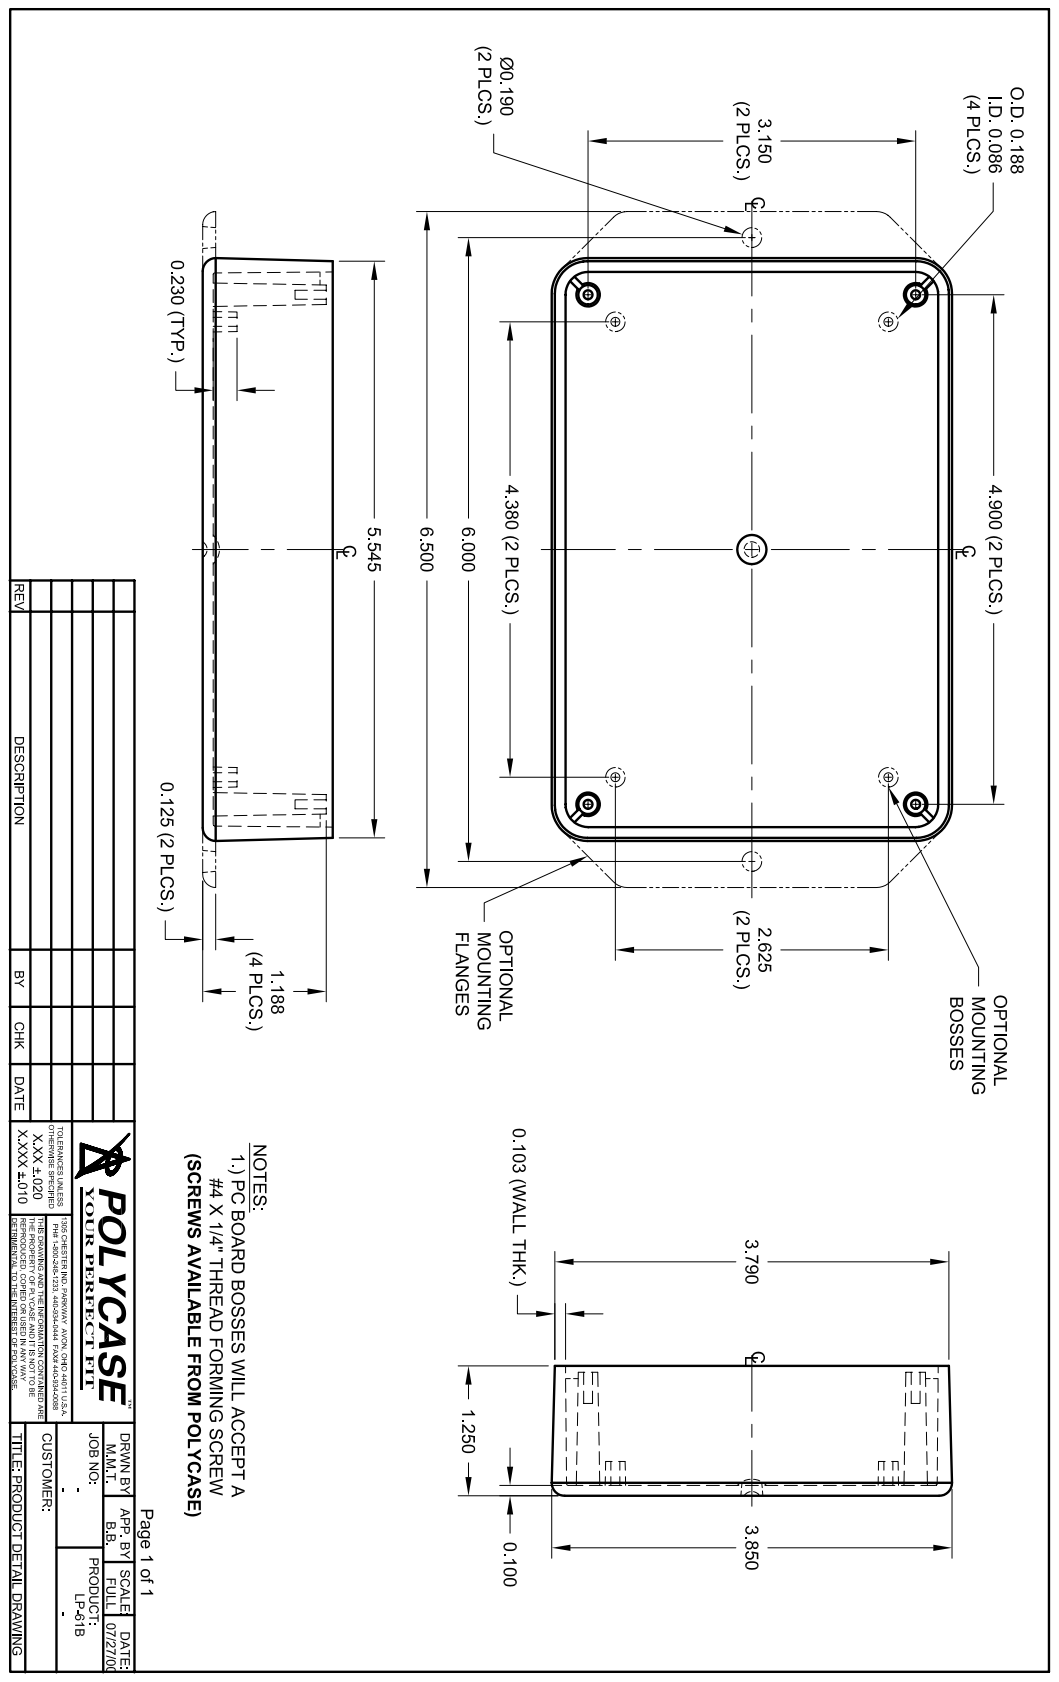
[picture p103: page 1]

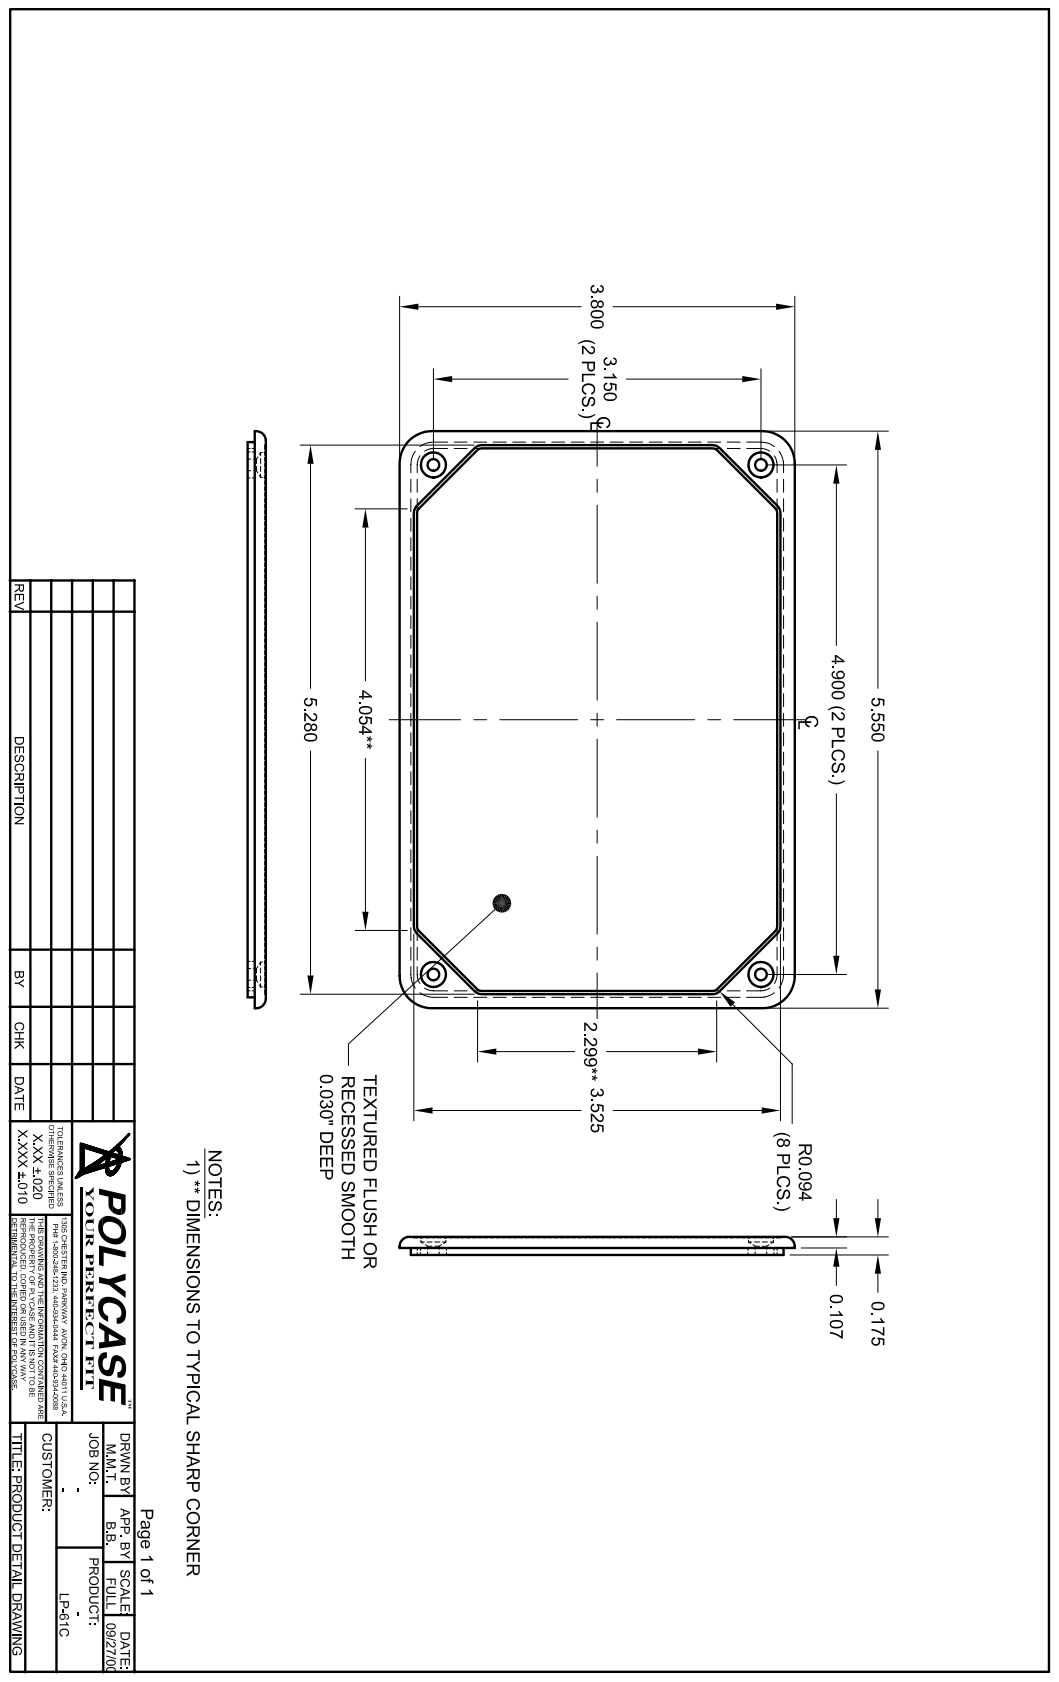
[picture p104: page 2]
