digamesystems/LIDAR/src/include/Digame/digameDisplay.h

/*Functions for using the Adafruit 1.54" Monochrome eInk Display. 
 * 
 * See: https://www.adafruit.com/product/4196
 * 
 */

#ifndef __DIGAME_DISPLAY_H__
#define __DIGAME_DISPLAY_H__

// base class GxEPD2_GFX can be used to pass references or pointers to the display 
// instance as parameter, uses ~1.2k more code
// enable or disable GxEPD2_GFX base class

#define ENABLE_GxEPD2_GFX 1 // Took me a longer than it should have to find this! --

#include <digameDebug.h>
#include <GxEPD2_BW.h>
#include <EEPROM.h>

//#include "GxEPD2_display_selection.h"

// Our pinouts to the Adafruit display.
#define EPD_DC 5     // can be any pin, but required!
#define EPD_CS 26    // can be any pin, but required!
#define EPD_BUSY 2   // can set to -1 to not use a pin (will wait a fixed delay)
#define SRAM_CS 27   // can set to -1 to not use a pin (uses a lot of RAM!)
#define SD_CS 14     // SD card chip select
#define EPD_RESET -1 // can set to -1 and share with chip Reset (can't deep sleep)

#define debugUART Serial

// Just grabbed the constructors we need from GxEPD2_display_selection and copied here.

// ADAFRUIT 1.54" ePaper Display. SSD1608
GxEPD2_BW<GxEPD2_154, GxEPD2_154::HEIGHT> display1(GxEPD2_154(/*CS=5*/ EPD_CS, /*DC=*/EPD_DC, /*RST=*/EPD_RESET, /*BUSY=*/EPD_BUSY)); // GDEH0154D67

// ADAFRUIT 1.54" ePaper Display. SSD1681
GxEPD2_BW<GxEPD2_154_D67, GxEPD2_154_D67::HEIGHT> display2(GxEPD2_154_D67(/*CS=5*/ EPD_CS, /*DC=*/EPD_DC, /*RST=*/EPD_RESET, /*BUSY=*/EPD_BUSY)); // GDEW0154M09 200x200

// ADAFRUIT 2.13" ePaper Display. 
GxEPD2_BW<GxEPD2_213_B72, GxEPD2_213_B72::HEIGHT> display3(GxEPD2_213_B72(/*CS=5*/ EPD_CS, /*DC=*/EPD_DC, /*RST=*/EPD_RESET, /*BUSY=*/EPD_BUSY)); // 


//GxEPD2_GFX& display = display2;
String displayType = "154_SSD1681";

GxEPD2_GFX *mainDisplay;


//******************************************************************************************
GxEPD2_GFX &getDisplay()
{ // So we can use different displays.
  if (displayType == "154_SSD1608")
  {
    return display1;//3; //1
  }
  
  if (displayType == "154_SSD1608")
  
  {
    return display2;
  }
  
  if (displayType == "213_SSD1608")
  {
    return display3;
  }

}

void initDisplay()
{
  bool changeDisplayType = false; 

  DEBUG_PRINTLN("  Initializing eInk Display...");
  DEBUG_PRINTLN("  Reading EEPROM");

  EEPROM.begin(10);
  delay(1000);

  if (EEPROM.read(0)==255){
    DEBUG_PRINTLN("   ****Display Uninitialized****");
    changeDisplayType = true;
  }else{
    DEBUG_PRINTLN("  Current Display Type: " + String(EEPROM.read(0)));
    DEBUG_PRINT(  "    Change? y/[n] (You have 5 sec to decide) ");
    unsigned long t1 = millis();
    unsigned long t2 = t1;

    while (
            !(debugUART.available()) && 
            ((t2-t1)<5000)
          )
    {
      t2 = millis();
      delay(500); // wait for data from the user... 
      DEBUG_PRINT(".");
    }

    DEBUG_PRINTLN();

    if (debugUART.available()){
      String ynString = debugUART.readStringUntil('\n');
      ynString.trim();
      if (ynString == "y") {changeDisplayType = true;}
    }

  }

  if (changeDisplayType){
    DEBUG_PRINTLN("   Enter Display Type 1=154_SSD1608, 2=154_SSD1681, 3=213_SSD1608: ");
    
    while (!(debugUART.available())){
      delay(10); // wait for data from the user... 
    }

    String inString = debugUART.readStringUntil('\n');
    inString.trim();
    DEBUG_PRINT("   You entered: ");
    DEBUG_PRINTLN(inString);

    if (inString =="1"){
       displayType = "154_SSD1608";
       EEPROM.write(0,1);
       EEPROM.commit();
    }

    if (inString == "2"){
       displayType = "154_SSD1681";
       EEPROM.write(0,2);
       EEPROM.commit();
    }

    if (inString == "3"){
       displayType = "213_SSD1608";
       EEPROM.write(0,3);
       EEPROM.commit();
    }
  } 

  DEBUG_PRINT("    Display Type: ");
  DEBUG_PRINT(EEPROM.read(0));


  if (EEPROM.read(0)==1){displayType="154_SSD1608";}
  if (EEPROM.read(0)==2){displayType="154_SSD1681";}
  if (EEPROM.read(0)==3){displayType="213_SSD1608";}

  DEBUG_PRINT(" = ");
  DEBUG_PRINTLN(displayType);

  GxEPD2_GFX &display = getDisplay();
   
  display.init(0);
  display.fillScreen(GxEPD_WHITE);
  display.refresh(false); // full update
  
  display.setRotation(3);
  display.setTextSize(2);
  display.setTextColor(GxEPD_BLACK);
 
  return;
}

void showWhite(){
  GxEPD2_GFX &display = getDisplay();
  //display.clearScreen();
  display.refresh(false); // full update
  display.fillRect(0, 0, 250, 122, GxEPD_WHITE);
  while (display.nextPage());
}

void showBlack(){
  GxEPD2_GFX &display = getDisplay();
  display.clearScreen();
  display.refresh(false); // full update
  display.fillRect(0, 0, 250, 122, GxEPD_BLACK);
  while (display.nextPage());
}

//******************************************************************************************
#if defined(ESP8266) || defined(ESP32)
  #include <StreamString.h>
  #define PrintString StreamString
#else
  class PrintString : public Print, public String
  {
  public:
    size_t write(uint8_t data) override
    {
      return concat(char(data));
    };
  };
#endif

//******************************************************************************************
// Print a string on the display, centered, at a particular y value.
void centerPrint(String s, uint16_t y)
{
  GxEPD2_GFX &display = getDisplay();
  int16_t tx, ty;
  uint16_t tw, th;
  display.getTextBounds(s, 0, 0, &tx, &ty, &tw, &th);
  uint16_t utx = ((display.width() - tw) / 2) - tx;
  uint16_t uty = y; //((display.height() - th) / 2) - ty;
  display.setCursor(utx, uty);
  display.print(s);
}

//******************************************************************************************
void displayTitles(String title1, String title2)
{
  GxEPD2_GFX &display = getDisplay();
  display.fillScreen(GxEPD_WHITE);
  //display.clearScreen();
  display.setTextSize(3);
  centerPrint(title1, 5);
  display.setTextSize(2);
  centerPrint(title2, 35);
}

//******************************************************************************************
void displayCopyright()
{
  GxEPD2_GFX &display = getDisplay();
  display.setTextSize(1);
  centerPrint("HEIMDALL VCS Family", 170);
  centerPrint("(c) 2021, Digame Systems.", 180);
  centerPrint("All rights reserved.", 190);
  //display.display();
  while (display.nextPage());
}

//******************************************************************************************
void displaySplashScreen(String s, String swVersion)
{
  displayTitles("HEIMDALL", s);
  centerPrint("Vehicle", 70);
  centerPrint("Counting System", 90);
  centerPrint("Version", 110);
  centerPrint(swVersion, 130);
  displayCopyright();
}

//******************************************************************************************
void displayIPScreen(String s)
{
  displayTitles("NETWORK", "");
  centerPrint("IP Address", 75);
  centerPrint(s, 100);
  displayCopyright();
}

//******************************************************************************************
void displayAPScreen(String ssid, String ip)
{
  displayTitles("NETWORK", "(ACCESS POINT)");
  centerPrint("SSID", 70);
  centerPrint(ssid, 90);
  centerPrint("IP Address", 115);
  centerPrint(ip, 135);
  displayCopyright();
}

//******************************************************************************************
void displayTextScreen(String title, String s)
{
  //initDisplay();
  GxEPD2_GFX &display = getDisplay();
  //display.fillScreen(GxEPD_WHITE);
  display.setTextSize(3);
  centerPrint(title, 10);
  display.setTextSize(2);
  centerPrint(s,45);
  displayCopyright();
}

//******************************************************************************************
// Display a title and 2 lines of centered text.
void displayTextScreen(String title, String s1, String s2)
{
  GxEPD2_GFX &display = getDisplay();
  display.setTextSize(3);
  centerPrint(title, 10);
  display.setTextSize(2);
  centerPrint(s1, 55);
  centerPrint(s2, 75);
  displayCopyright();
}

//******************************************************************************************
void displayTextScreenLarge(String title, String s)
{
  GxEPD2_GFX &display = getDisplay();
  display.setTextSize(3);
  centerPrint(title, 10);
  centerPrint(s,60);
  displayCopyright();
}

//******************************************************************************************
void displayStatusScreen(String s)
{
  displayTextScreen("SELF-TEST", s);
}

//******************************************************************************************
void displayEventScreen(String s)
{
  displayTextScreen("EVENT", s);
}

//******************************************************************************************
void displayCountScreen(double v)
{
  displayTitles("COUNTS", "");
  displayCopyright();
}

//******************************************************************************************
void displayCountersSummaryScreen(String total, String summary)
{
  GxEPD2_GFX &display = getDisplay();  
  displayTitles("SUMMARY", "Total: " + total);
  display.setCursor(0, 70);
  display.print(summary);
  displayCopyright();
}

//******************************************************************************************
void displayBarcodeScreen()
{
  initDisplay();
  GxEPD2_GFX &display = getDisplay();  
}


//******************************************************************************************
void showValue(double v)
{
  GxEPD2_GFX &display = getDisplay();
  int digits = 0;

  display.setTextSize(5);
  display.setTextColor(GxEPD_BLACK);

  PrintString valueString;
  valueString.print(v, digits);

  int16_t tbx, tby;
  uint16_t tbw, tbh;
  display.getTextBounds(valueString, 0, 0, &tbx, &tby, &tbw, &tbh);

  uint16_t x = ((display.width() - tbw) / 2) - tbx;
  uint16_t y = ((display.height() - tbh) / 2) - tby; //+ tbh / 2; // y is base line!

  // show what happens, if we use the bounding box for partial window
  uint16_t wx = (display.width() - tbw) / 2;
  uint16_t wy = (display.height() - tbh) / 2; // / 2;

  display.setPartialWindow(wx, wy, tbw, tbh);
  display.firstPage();
  do
  {
    display.fillScreen(GxEPD_WHITE);
    display.setCursor(x, y);
    display.print(valueString);
  } while (display.nextPage());
  //See if we can put things back the way we found them
  display.setPartialWindow(0, 0, display.width(), display.height());
  display.firstPage();
}

//******************************************************************************************
void showPartialXY(String msg, int x, int y)
{
  GxEPD2_GFX &display = getDisplay();
  int digits = 0;

  display.setTextSize(3);
  display.setTextColor(GxEPD_BLACK);

  int16_t tbx, tby;
  uint16_t tbw, tbh;
  display.getTextBounds(msg, 0, 0, &tbx, &tby, &tbw, &tbh);

  //uint16_t x = ((display.width() - tbw) / 2) - tbx;
  //uint16_t y = ((display.height() - tbh) / 2) - tby; //+ tbh / 2; // y is base line!

  // show what happens, if we use the bounding box for partial window
  //uint16_t wx = (display.width() - tbw) / 2;
  //uint16_t wy = (display.height() - tbh) / 2; // / 2;

  display.setPartialWindow(x, y, tbw, tbh);
  display.firstPage();
  do
  {
    //display.fillScreen(GxEPD_WHITE);
    display.setCursor(x, y);
    display.print(msg);
  } while (display.nextPage());

  //Put things back the way we found them
  display.setPartialWindow(0, 0, display.width(), display.height());
  display.firstPage();
}

#endif //__DIGAME_DISPLAY_H__
