digamesystems/LIDAR/src/include/Digame/digamePowerMgt.h

/*
  Power management functions
*/
#ifndef __DIGAME_POWER_MGT_H__
#define __DIGAME_POWER_MGT_H__

#include <WiFi.h>         // WiFi stack
#include "driver/adc.h"   // ADC functions. (Allows us to turn off to save power.)
#include <esp_bt.h>       // Bluetooth control functions
#include <esp_wifi.h>

#define debugUART Serial



//*****************************************************************************
// Sleep the ESP32 
void lightSleepMSec(unsigned long ms){
  unsigned long mS_TO_S_FACTOR = 1000;
  esp_sleep_enable_timer_wakeup(ms * mS_TO_S_FACTOR);
  esp_light_sleep_start(); 
}

//*****************************************************************************
// Disable Bluetooth, the ADC sub-system, WiFi and drop the CPU down to 40Mhz.
void setLowPowerMode() {
    debugUART.print("  Switching to Low Power Mode... ");
    WiFi.disconnect(true);
    WiFi.mode(WIFI_OFF);
    btStop();
    adc_power_off();
    esp_wifi_stop();
    esp_bt_controller_disable();
    debugUART.println("40 MHz");
    setCpuFrequencyMhz(40); // Slow down the CPU
    debugUART.println("    Done. Low Power Mode Enabled.");
}

//*****************************************************************************
// Disable Bluetooth, the ADC sub-system, and drop the CPU down to 80MHz.
// Leave WiFi active. 
void setMediumPowerMode() {
    debugUART.print("  Switching to Medium Power Mode... ");
    btStop();
    //adc_power_off();
    esp_bt_controller_disable();
    setCpuFrequencyMhz(80); // Slow down the CPU
    debugUART.println("    Done. Medium Power Mode Enabled.");
}

//***************************************************************************** 
// Run the CPU Flat out at 240MHz w/ WiFi active. Turn off and Bluetooth.
void setFullPowerMode() {
    debugUART.println("  Switching to Full Power Mode... ");
    setCpuFrequencyMhz(240); // Speed up the CPU
    btStop();
    esp_bt_controller_disable();
    adc_power_on();          // Turn on the ADCs for WiFi
    debugUART.println("    Done. Full Power Mode Enabled. ");
}

#endif 
