digamesystems/LIDAR/images/20210716_140126.jpg

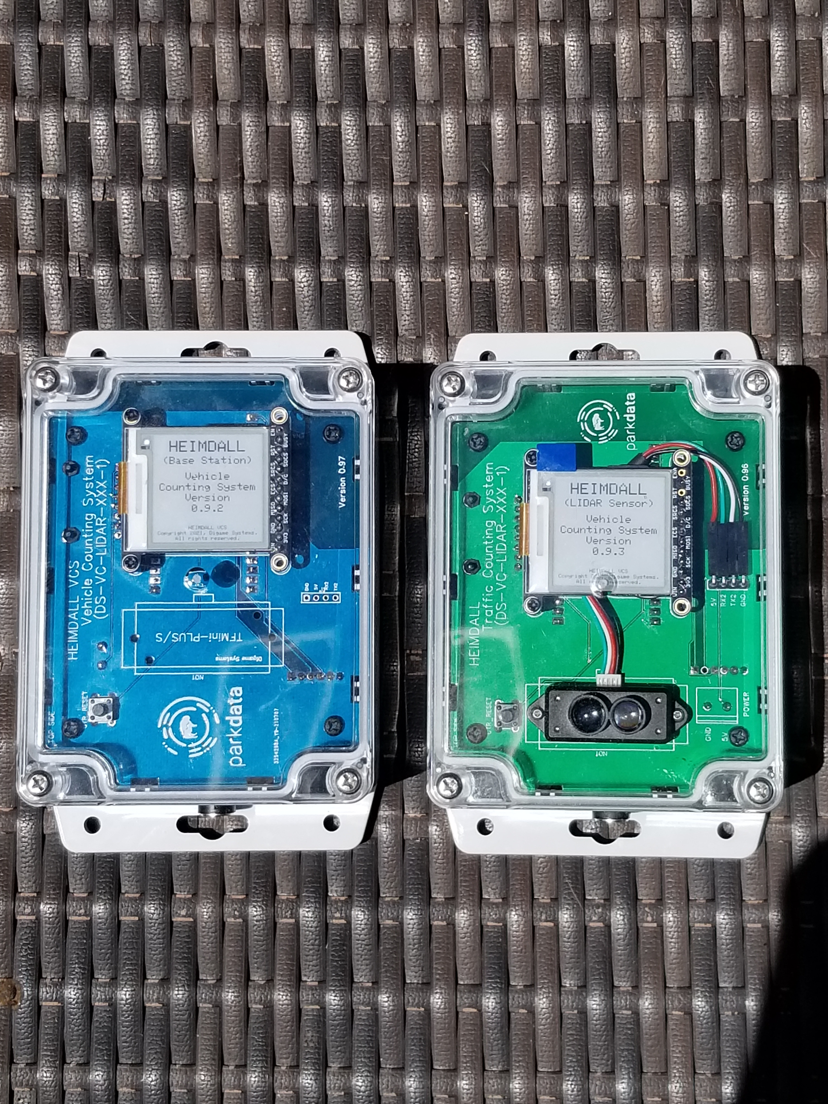
images/20210716_140126.jpg
