digamesystems/LIDAR/images/Shuttle Counter/20210423_175311.jpg

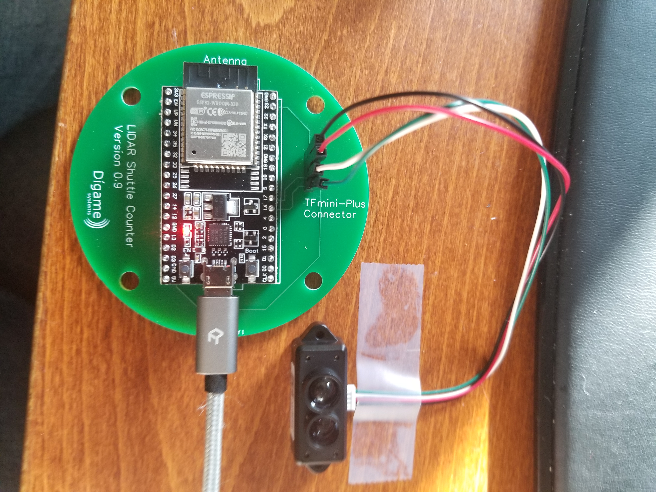
images/Shuttle Counter/20210423_175311.jpg
