digamesystems/LIDAR/images/Shuttle Counter/20211229_120249.jpg

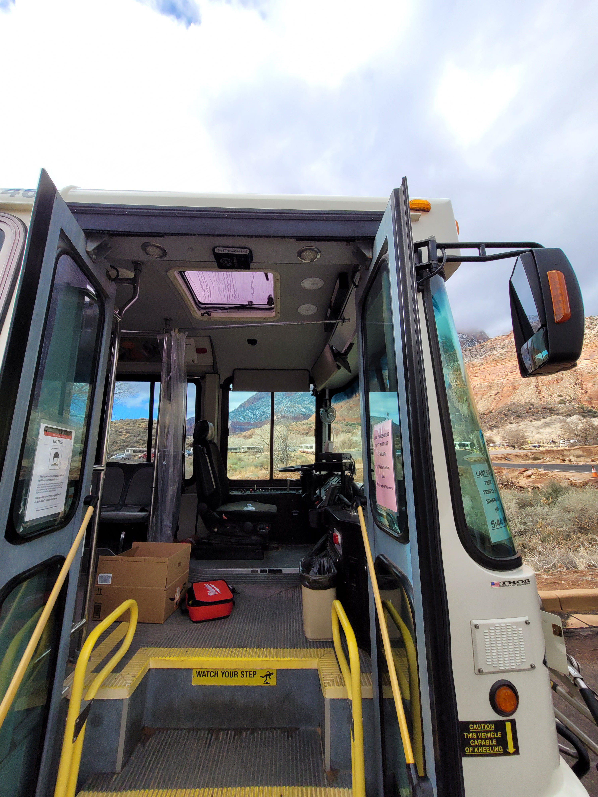
images/Shuttle Counter/20211229_120249.jpg
