digamesystems/LIDAR/images/Shuttle Counter/PXL_20210416_000328806.jpg

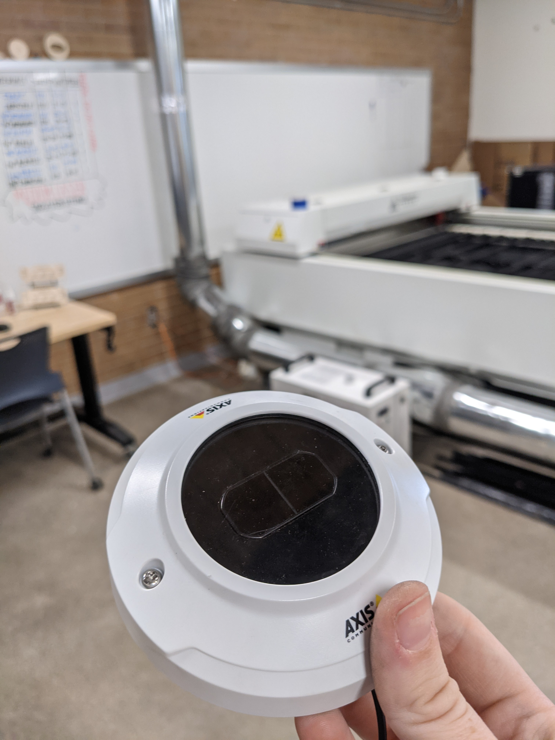
images/Shuttle Counter/PXL_20210416_000328806.jpg
