digamesystems/LIDAR/images/Shuttle Counter/PXL_20210510_175928390.jpg

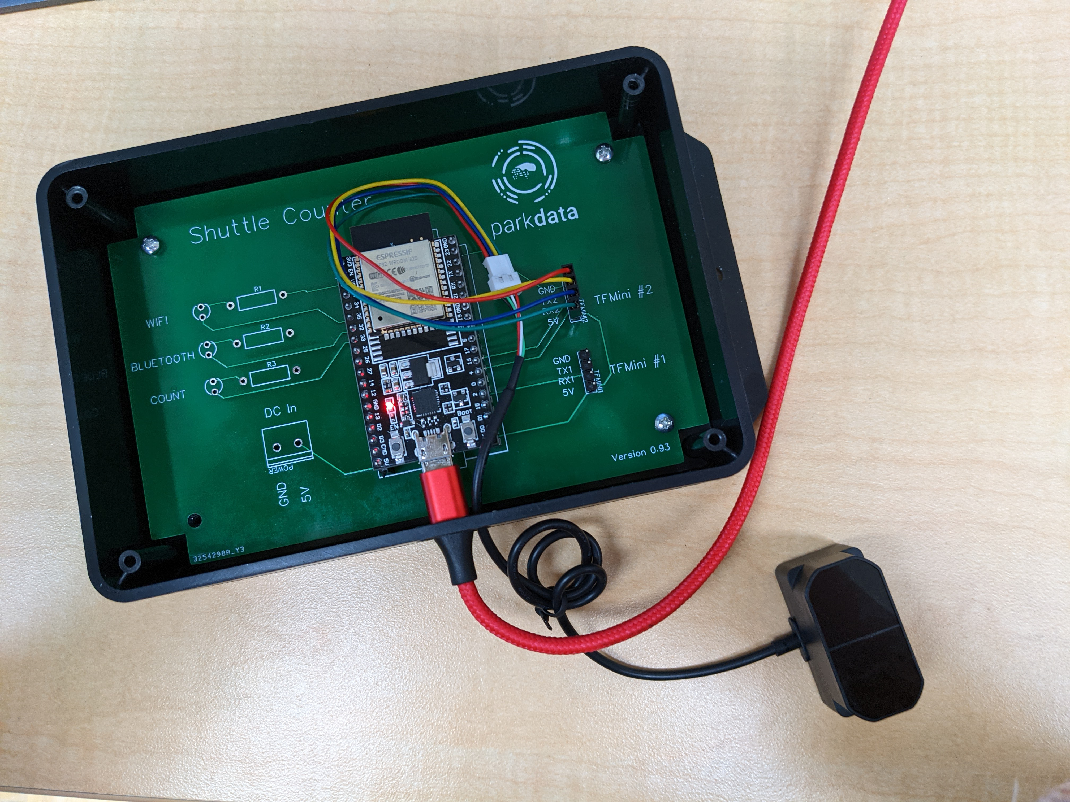
images/Shuttle Counter/PXL_20210510_175928390.jpg
