digamesystems/LIDAR/images/Shuttle Counter/shuttle_lidar_prototype.jpg

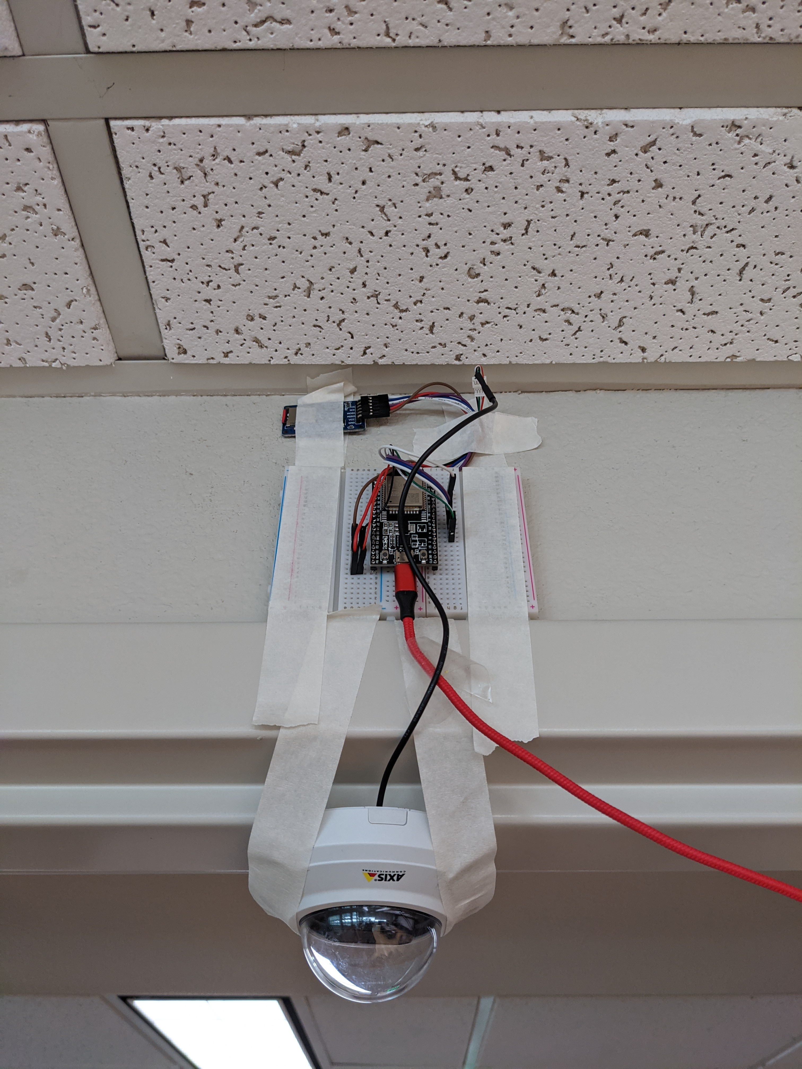
images/Shuttle Counter/shuttle_lidar_prototype.jpg
