digamesystems/LIDAR/images/Vehicle Counter/20201228_114332.jpg

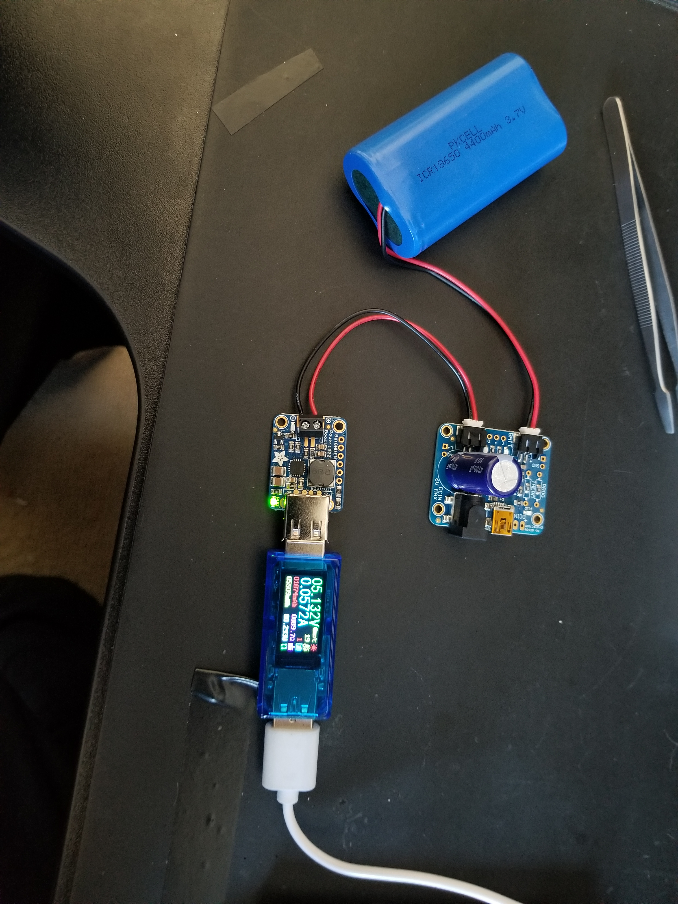
images/Vehicle Counter/20201228_114332.jpg
