digamesystems/LIDAR/images/Vehicle Counter/20201228_114651.jpg

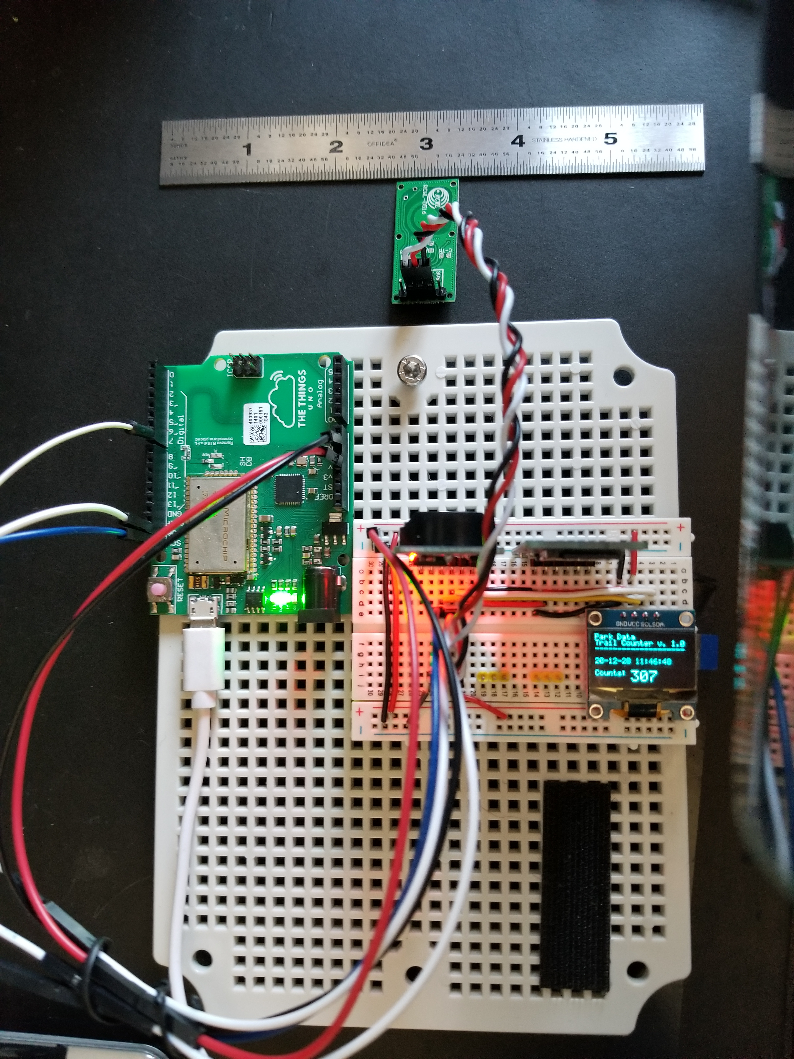
images/Vehicle Counter/20201228_114651.jpg
