digamesystems/LIDAR/images/Vehicle Counter/PXL_20210504_221816030.jpg

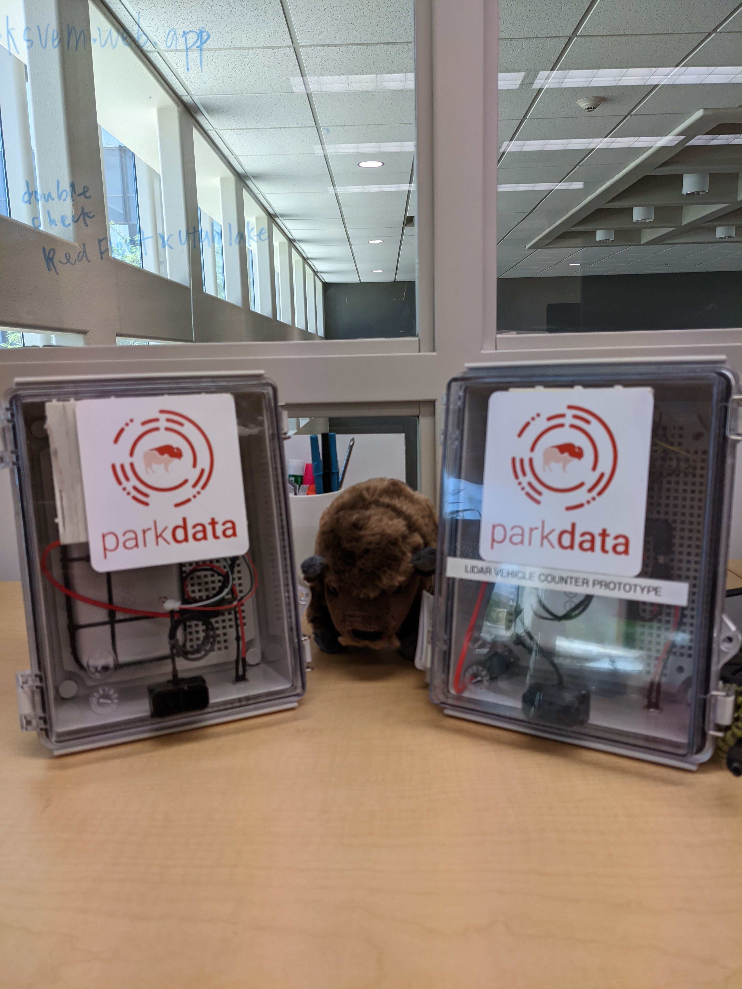
images/Vehicle Counter/PXL_20210504_221816030.jpg
