digamesystems/LIDAR/images/Vehicle Counter/PXL_20210504_221900099.jpg

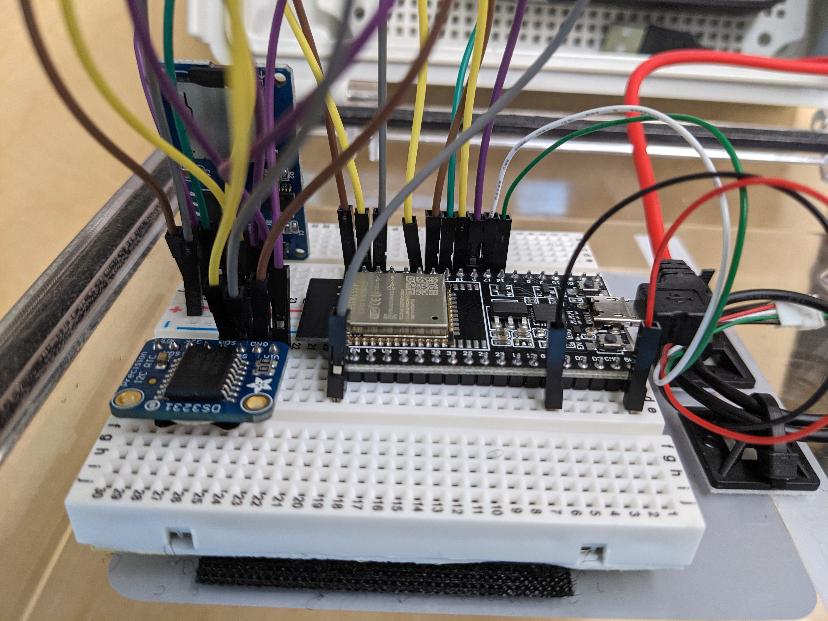
images/Vehicle Counter/PXL_20210504_221900099.jpg
